slopus/codex-keybored/cnc/vendor_response/2026-07-18_JLCCNC_laser_marking/CM2-002_LASER_PLACEMENT_PREVIEW_RevB.png

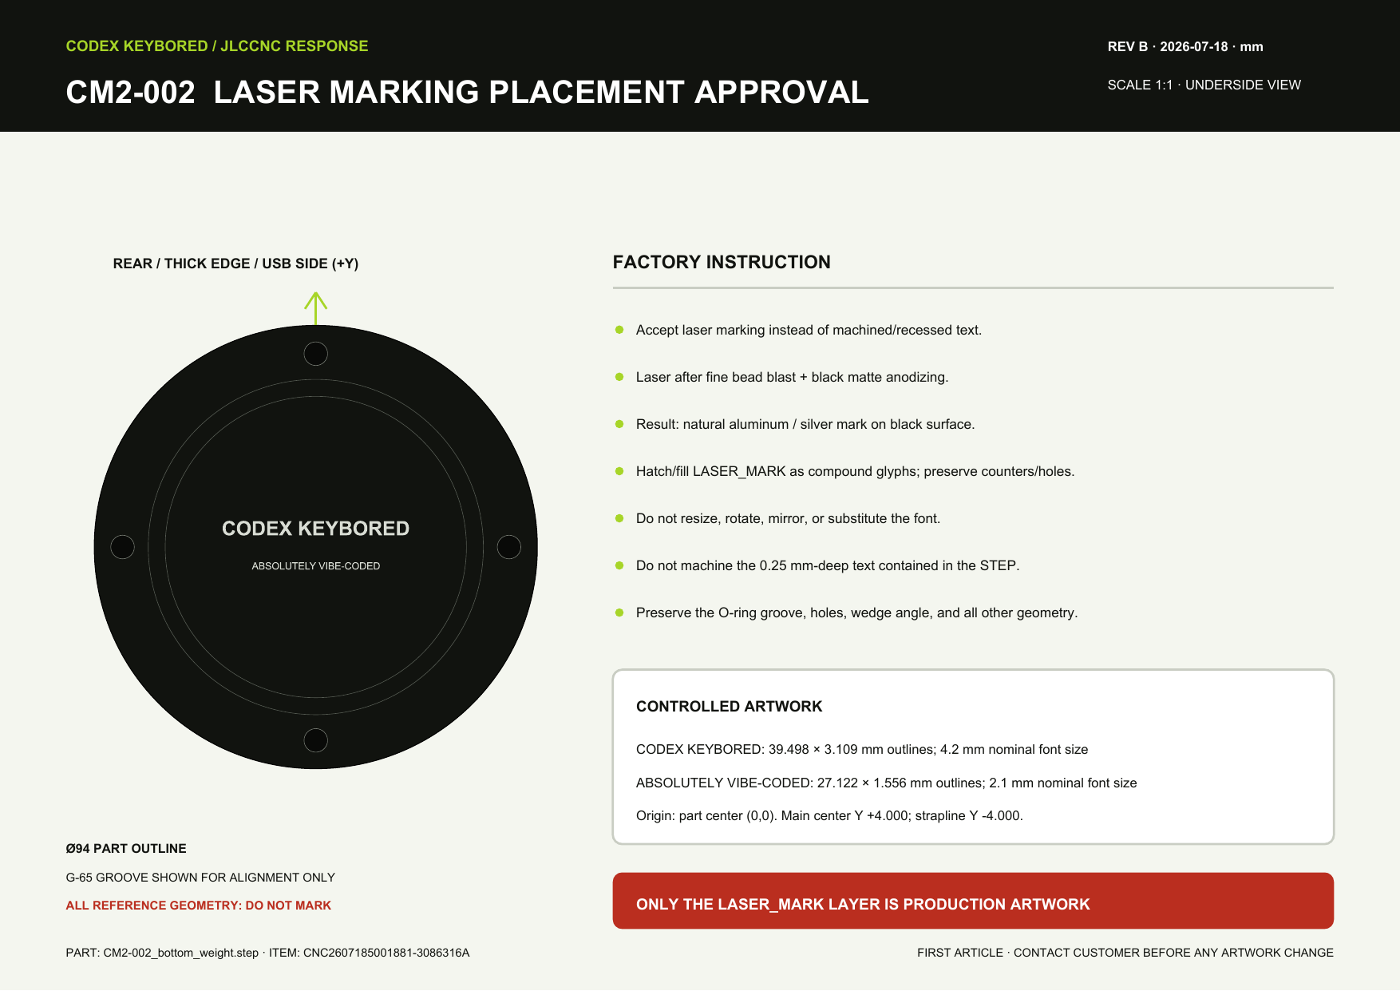
cnc/vendor_response/2026-07-18_JLCCNC_laser_marking/CM2-002_LASER_PLACEMENT_PREVIEW_RevB.png
