slopus/codex-keybored/docs/assets/jlcpcb/cart_pcb_cnc.png

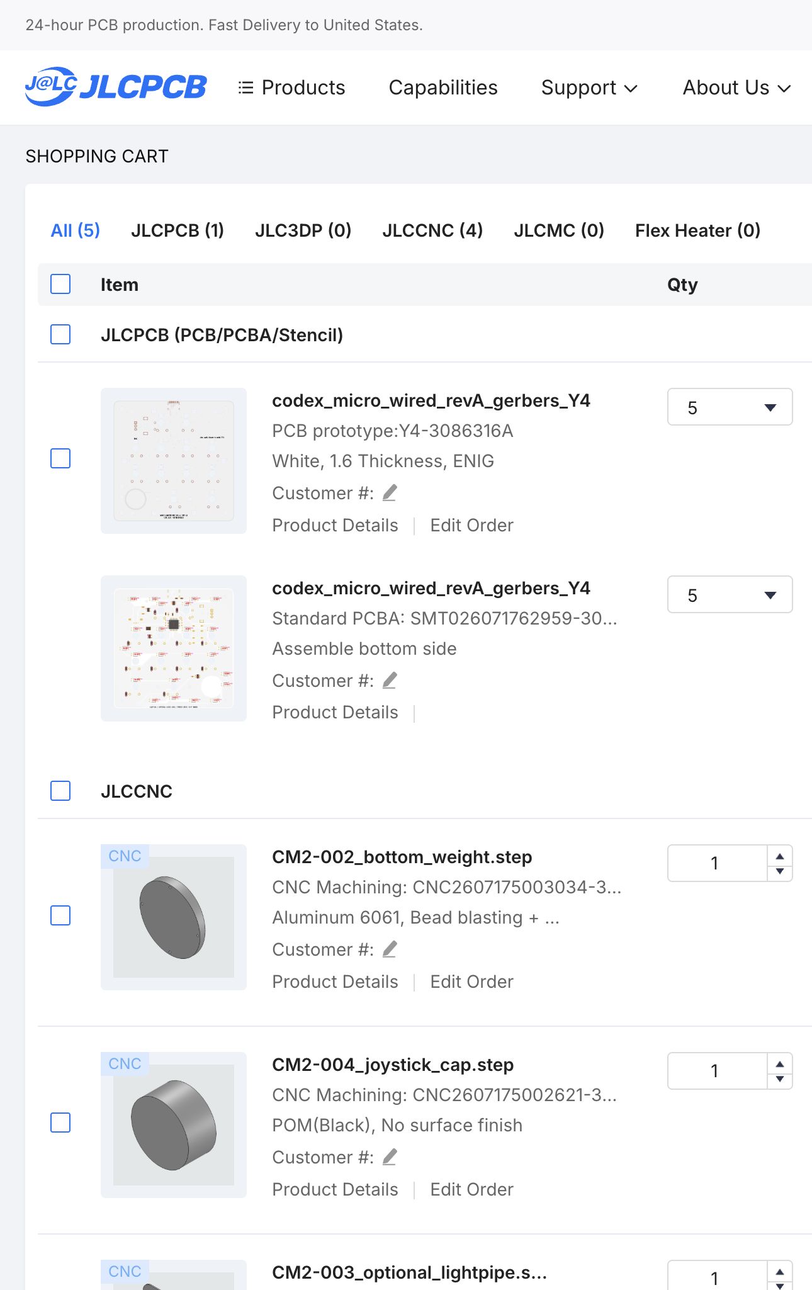
docs/assets/jlcpcb/cart_pcb_cnc.png
