slopus/codex-keybored/docs/assets/jlcpcb/cart_summary_total.png

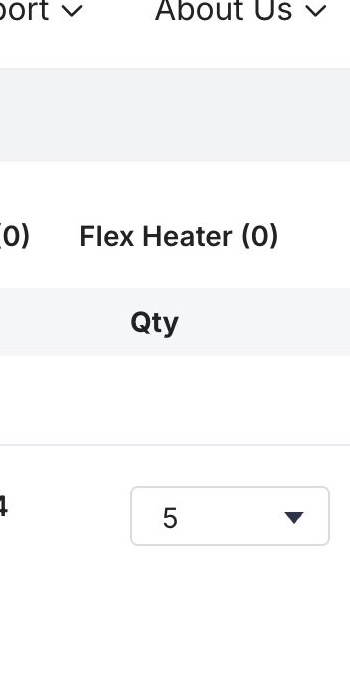
docs/assets/jlcpcb/cart_summary_total.png
