slopus/codex-keybored/docs/assets/jlcpcb/pcb_quote_config_full.png

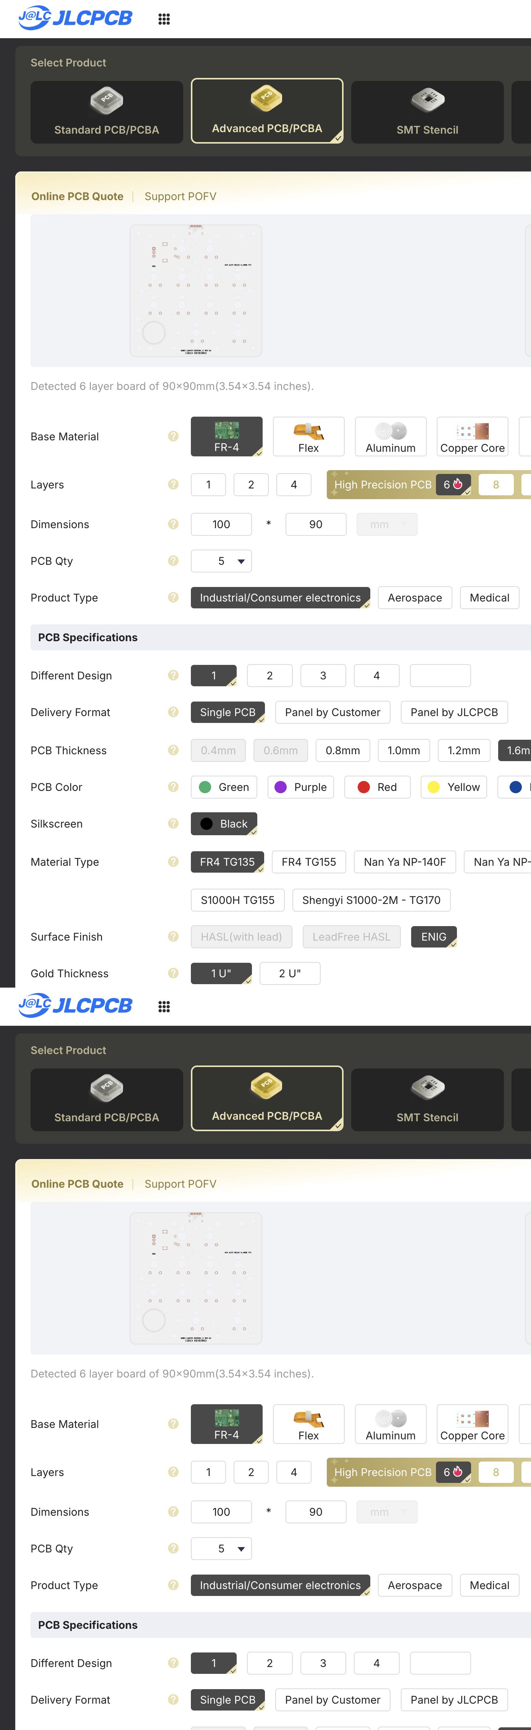
docs/assets/jlcpcb/pcb_quote_config_full.png
