slopus/codex-keybored/docs/assets/jlcpcb/pcba_final_quote.png

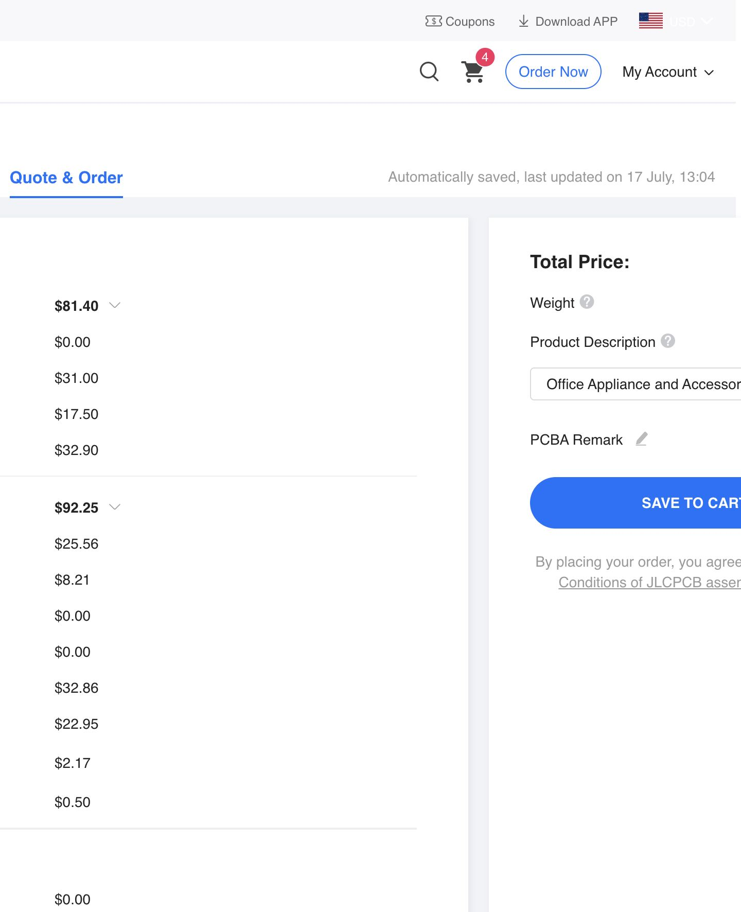
docs/assets/jlcpcb/pcba_final_quote.png
