slopus/codex-keybored/docs/assets/jlcpcb/pcba_final_quote_right.png

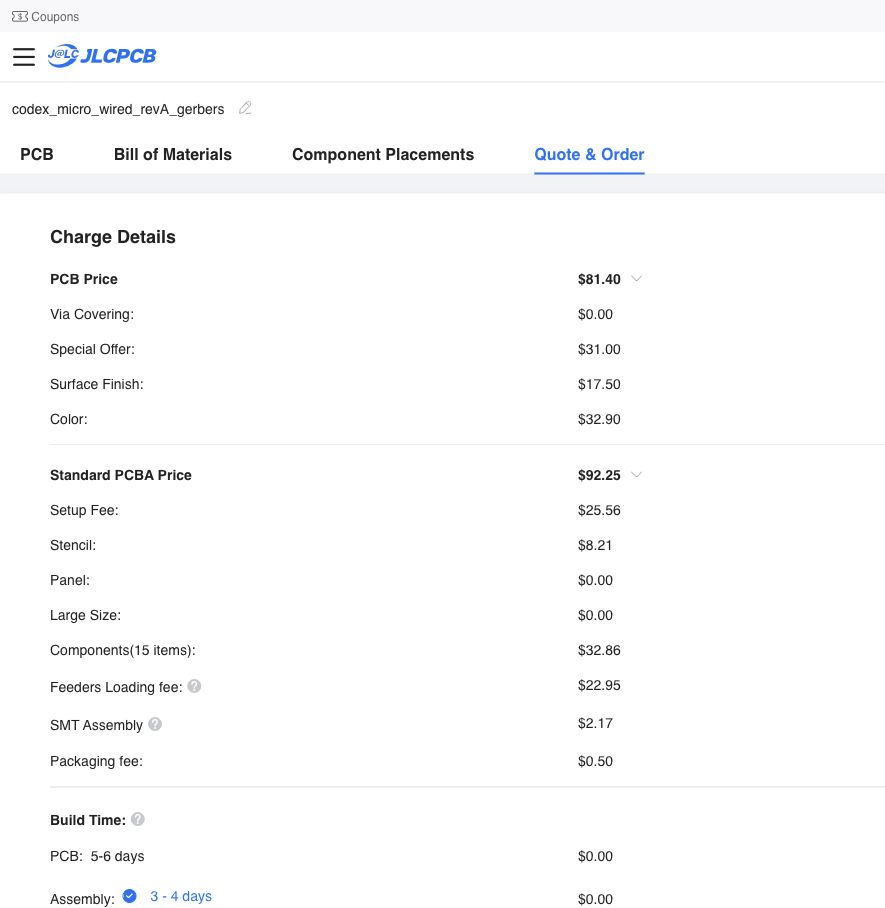
docs/assets/jlcpcb/pcba_final_quote_right.png
