slopus/codex-keybored/docs/assets/jlcpcb/pcba_final_total.png

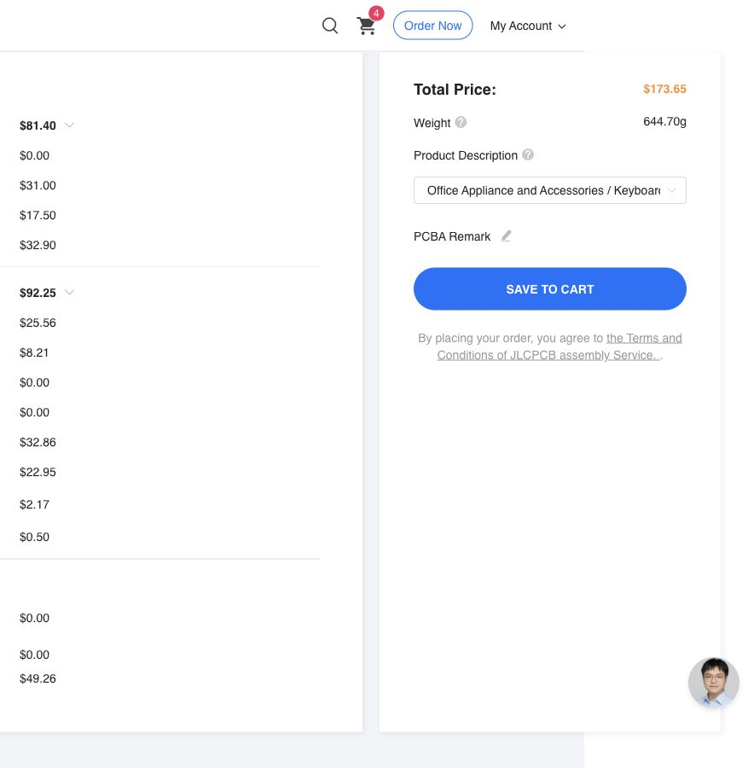
docs/assets/jlcpcb/pcba_final_total.png
