slopus/codex-keybored/docs/assets/jlcpcb/pcba_placement.png

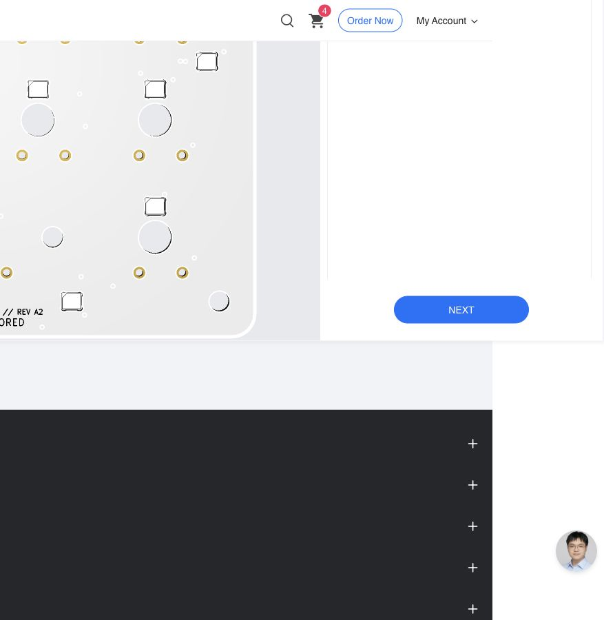
docs/assets/jlcpcb/pcba_placement.png
