slopus/codex-keybored/docs/assets/jlcpcb/turnkey_pcba_options.png

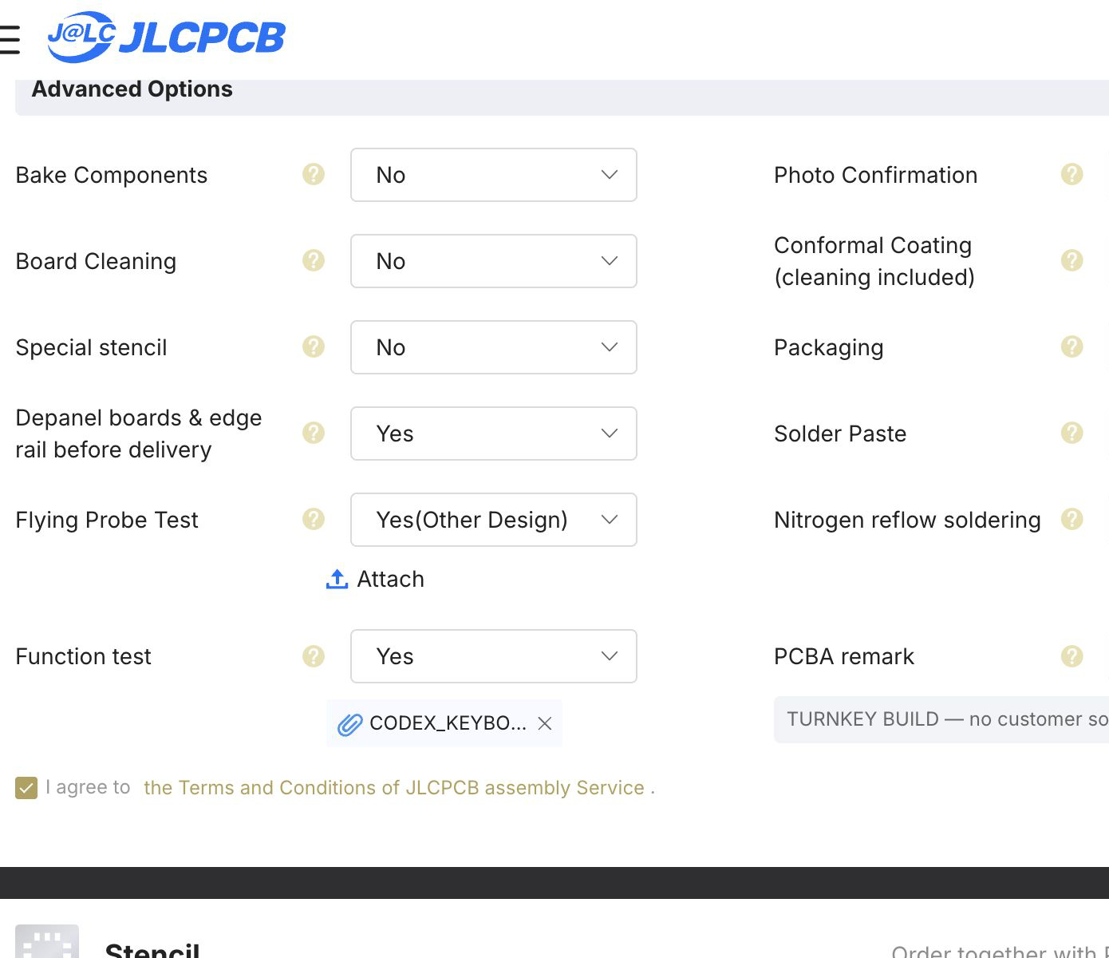
docs/assets/jlcpcb/turnkey_pcba_options.png
