slopus/codex-keybored/docs/assets/jlcpcb/turnkey_pcba_options_full.png

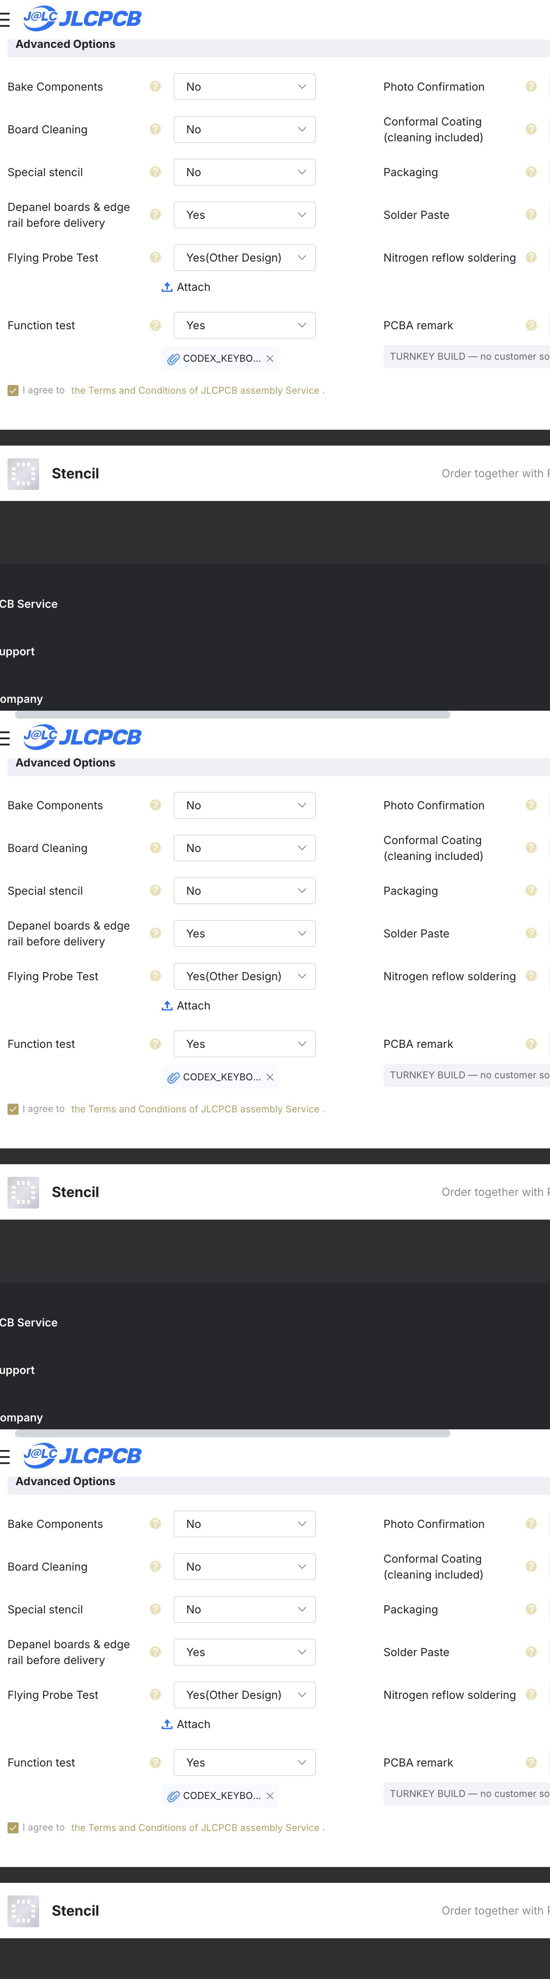
docs/assets/jlcpcb/turnkey_pcba_options_full.png
