slopus/codex-keybored/docs/assets/jlcpcb/turnkey_quote_total.png

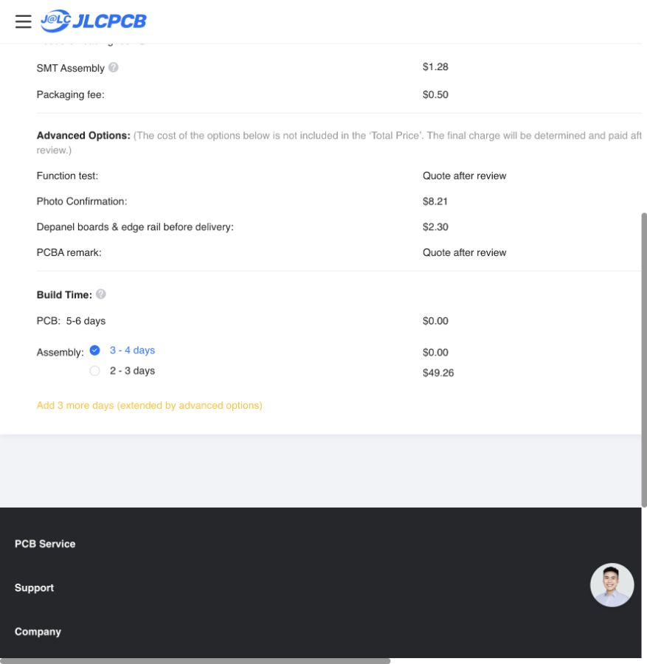
docs/assets/jlcpcb/turnkey_quote_total.png
