slopus/codex-keybored/docs/assets/pcb/keybored_bottom.png

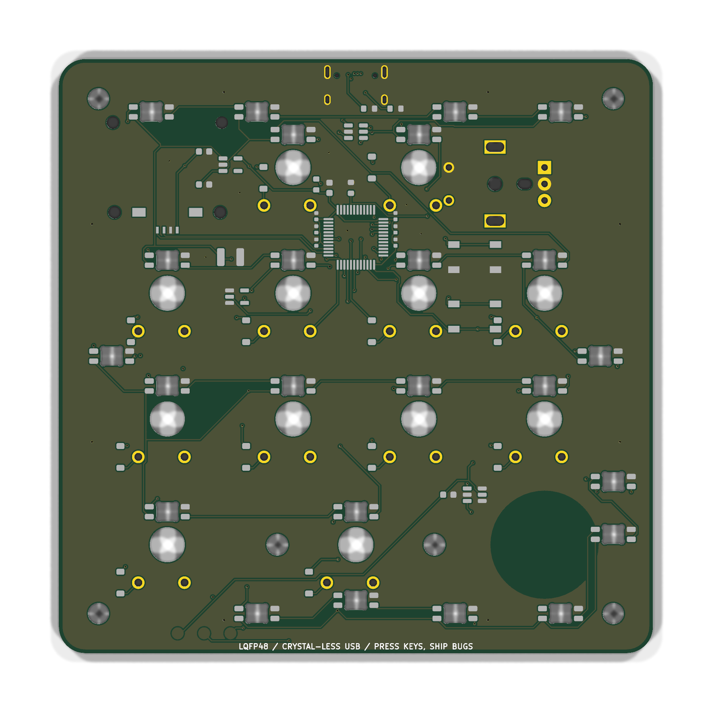
docs/assets/pcb/keybored_bottom.png
