slopus/codex-keybored/docs/assets/pcb/wired-reva-B-Cu.png

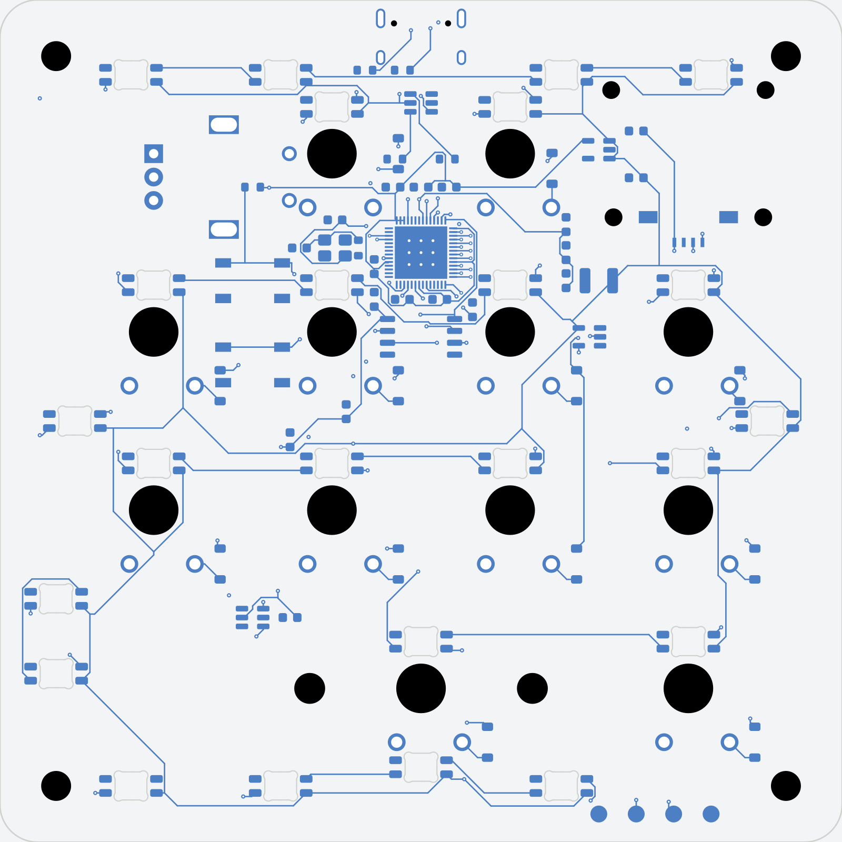
docs/assets/pcb/wired-reva-B-Cu.png
