slopus/codex-keybored/docs/assets/pcb/wired-reva-current-bottom.png

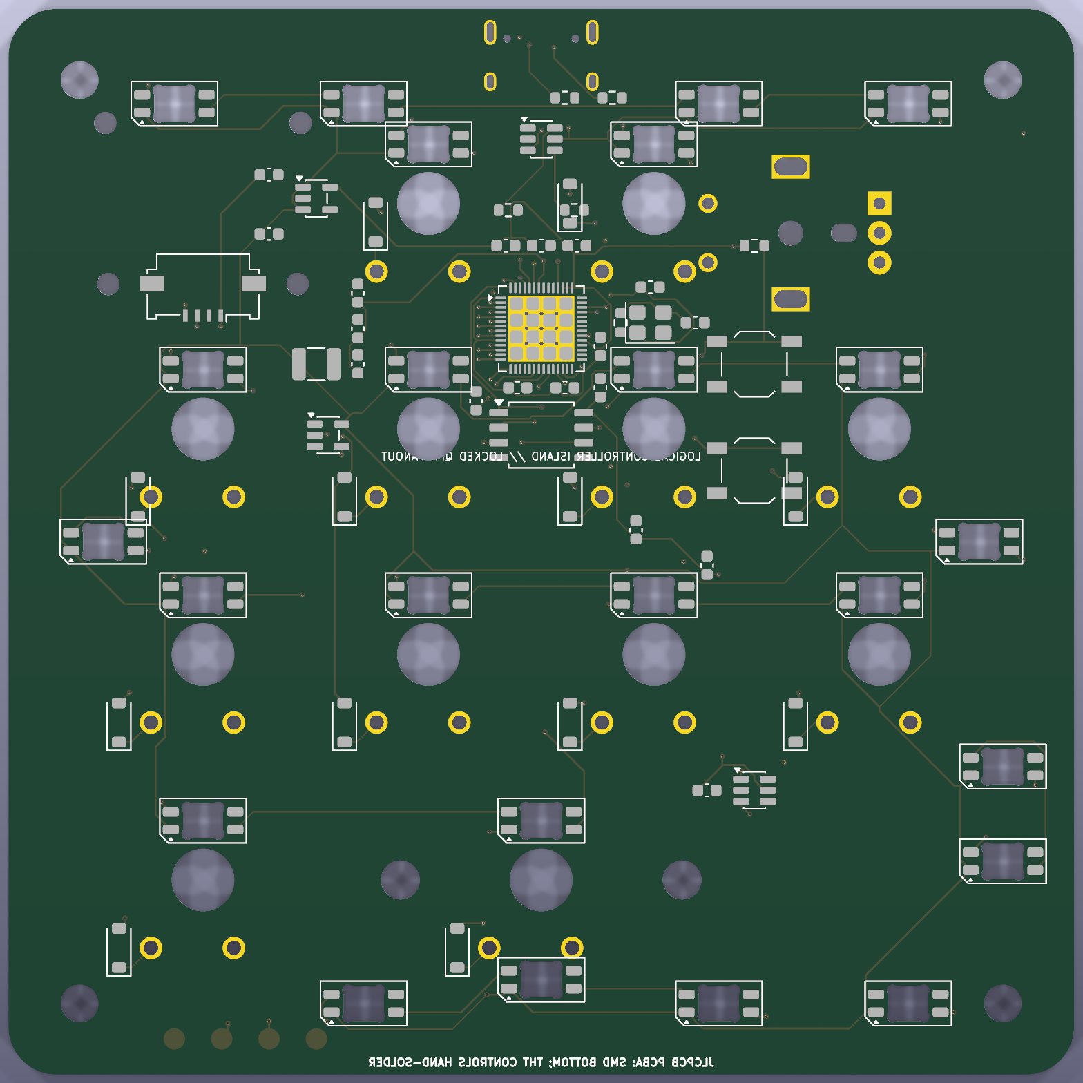
docs/assets/pcb/wired-reva-current-bottom.png
