slopus/codex-keybored/docs/assets/pcb/wired-reva-current-top.png

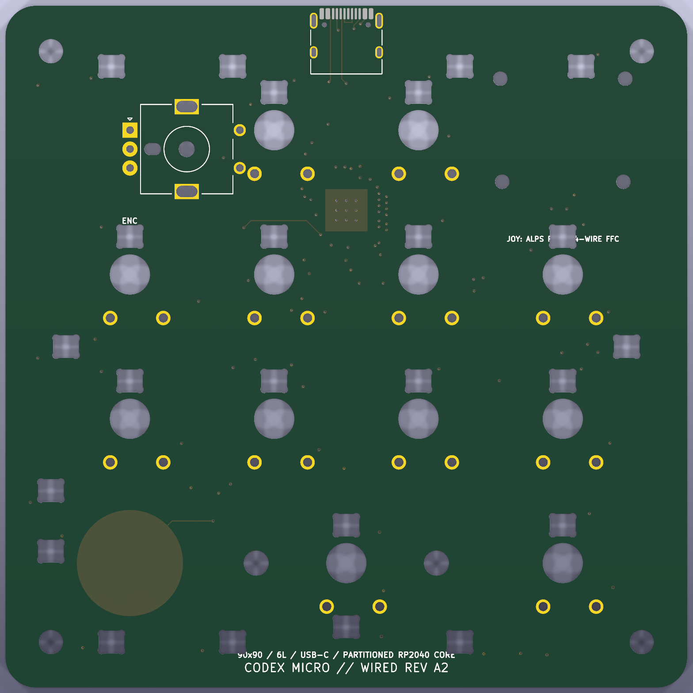
docs/assets/pcb/wired-reva-current-top.png
