slopus/codex-keybored/docs/assets/pcb/wired-reva-F-Cu.png

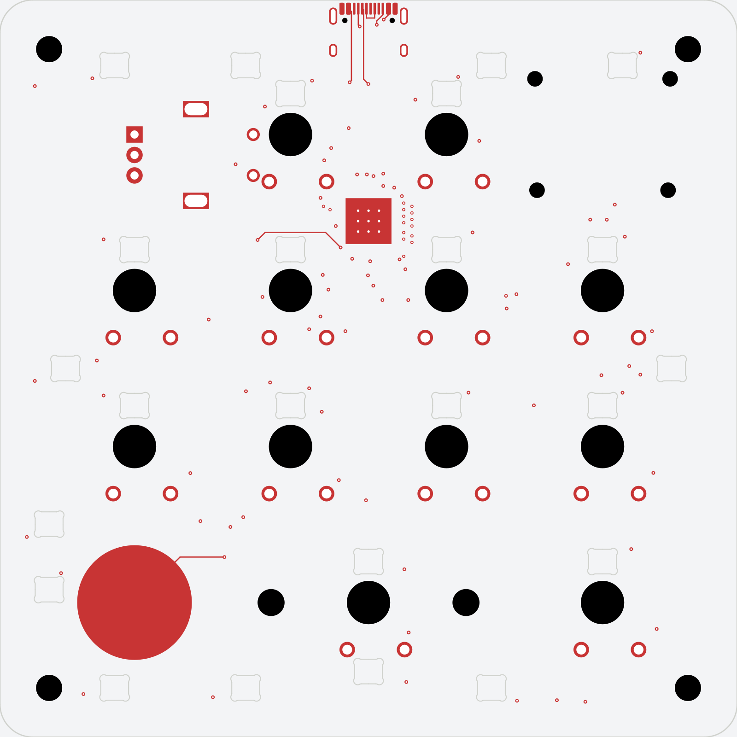
docs/assets/pcb/wired-reva-F-Cu.png
