slopus/codex-keybored/docs/assets/pcb/wired-reva-In1-Cu.png

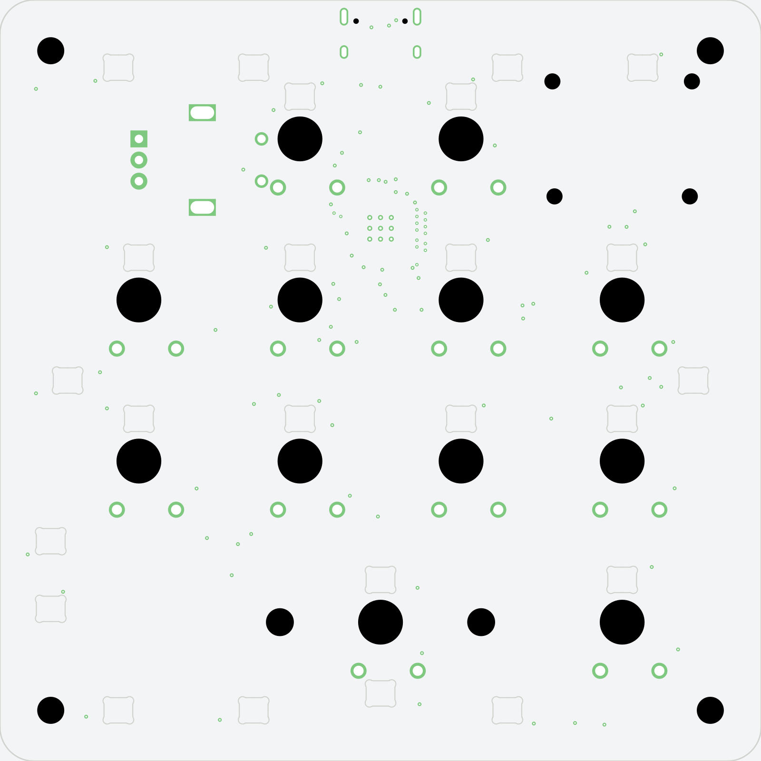
docs/assets/pcb/wired-reva-In1-Cu.png
