slopus/codex-keybored/docs/assets/pcb/wired-reva-In2-Cu.png

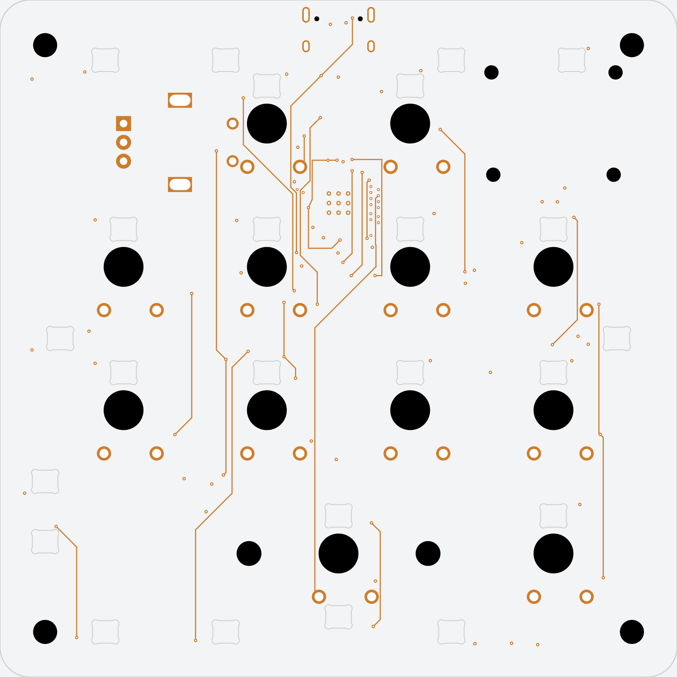
docs/assets/pcb/wired-reva-In2-Cu.png
