slopus/codex-keybored/docs/assets/pcb/wired-reva-In3-Cu.png

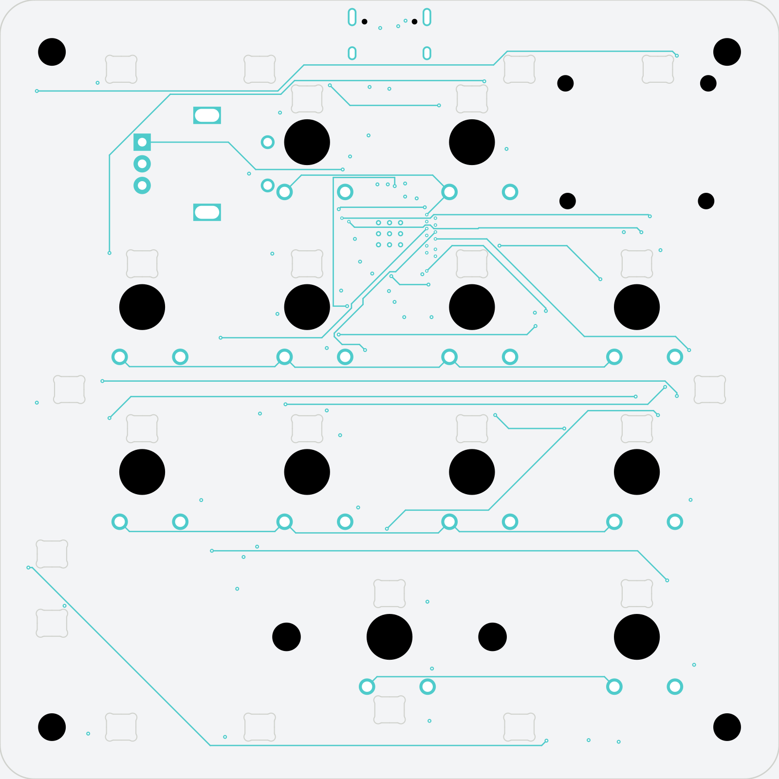
docs/assets/pcb/wired-reva-In3-Cu.png
