slopus/codex-keybored/docs/assets/renders/fusion-cm2-001-upper-housing.png

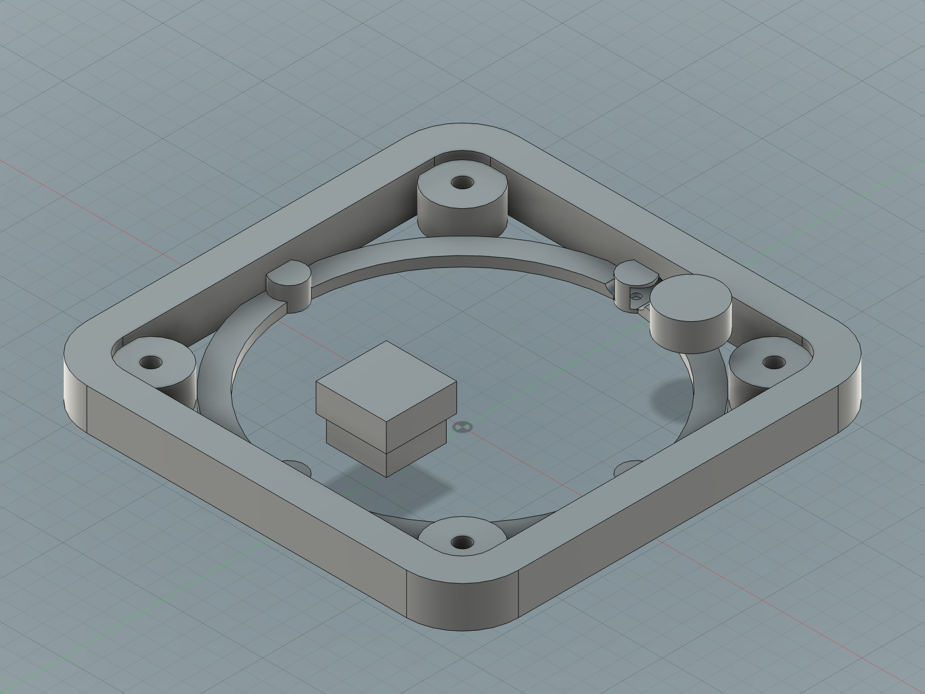
docs/assets/renders/fusion-cm2-001-upper-housing.png
