slopus/codex-keybored/docs/assets/renders/fusion-cm2-002-bottom-weight-side.png

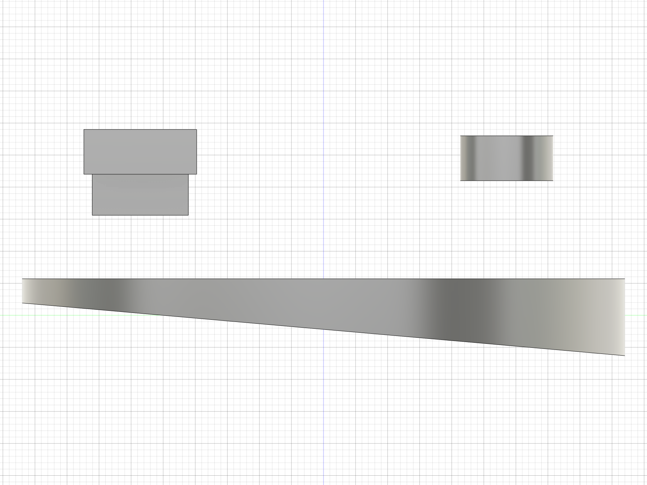
docs/assets/renders/fusion-cm2-002-bottom-weight-side.png
