slopus/codex-keybored/docs/assets/renders/fusion-cm2-002-bottom-weight.png

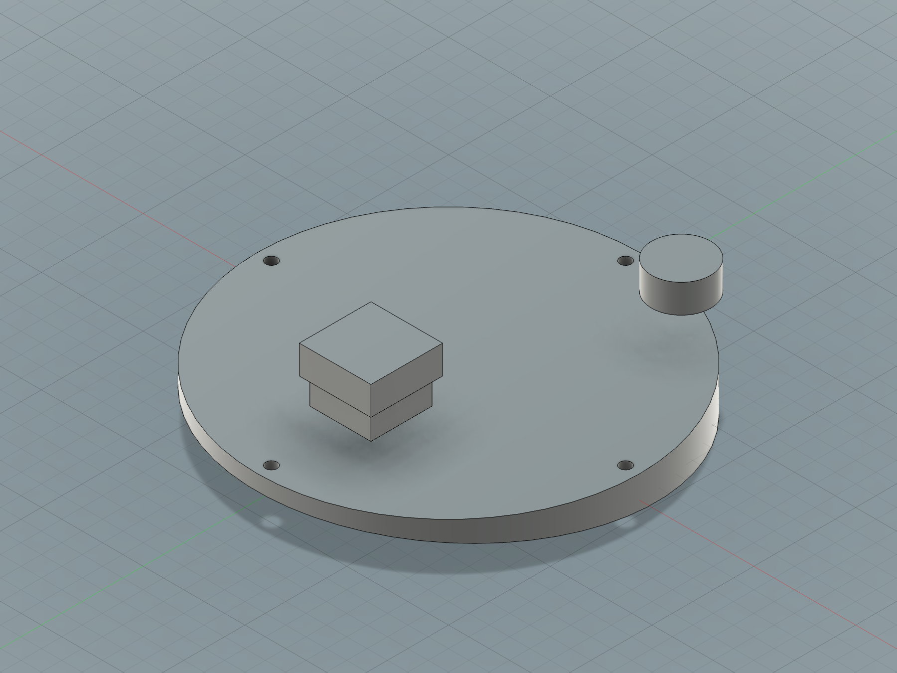
docs/assets/renders/fusion-cm2-002-bottom-weight.png
