slopus/codex-keybored/docs/assets/renders/fusion-cm2-004-joystick-cap.png

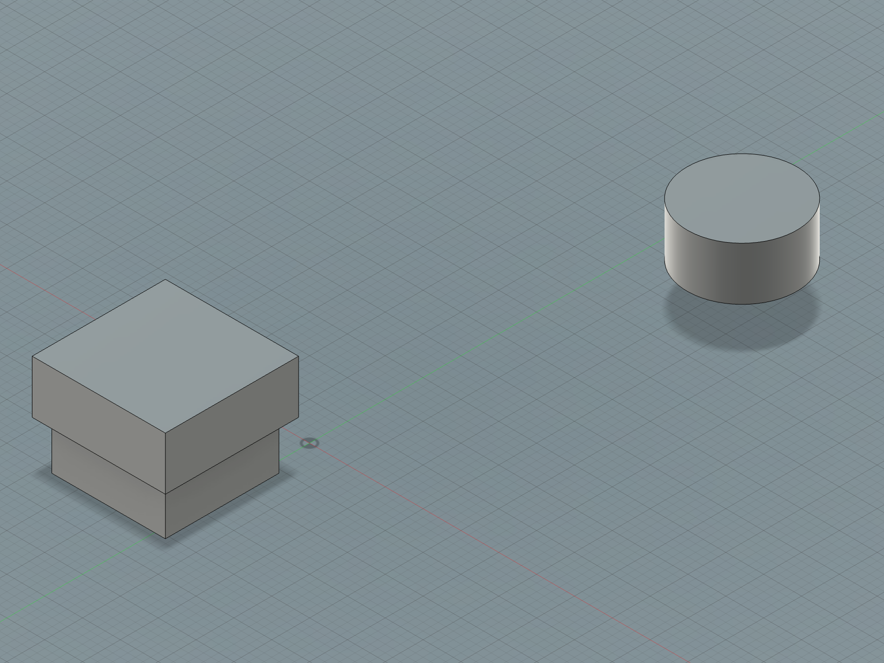
docs/assets/renders/fusion-cm2-004-joystick-cap.png
