slopus/codex-keybored/docs/assets/renders/kicad-wired-reva-top.png

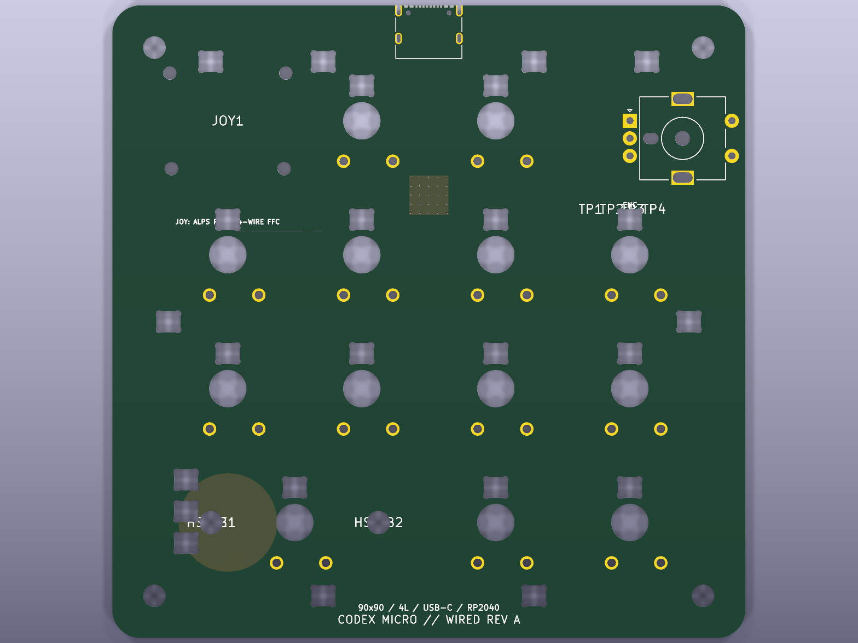
docs/assets/renders/kicad-wired-reva-top.png
