slopus/codex-keybored/docs/assets/renders/revb-cm2-001-upper.png

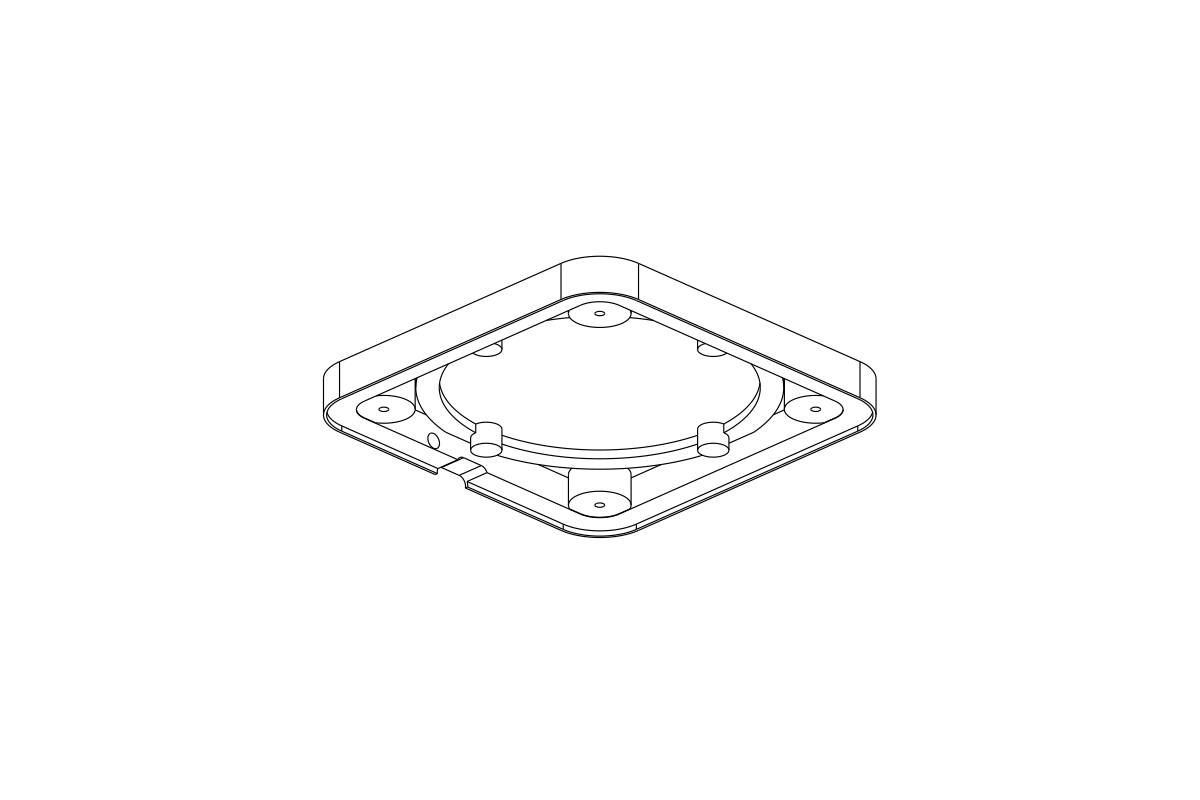
docs/assets/renders/revb-cm2-001-upper.png
