slopus/codex-keybored/docs/assets/renders/revb-cm2-002-bottom.png

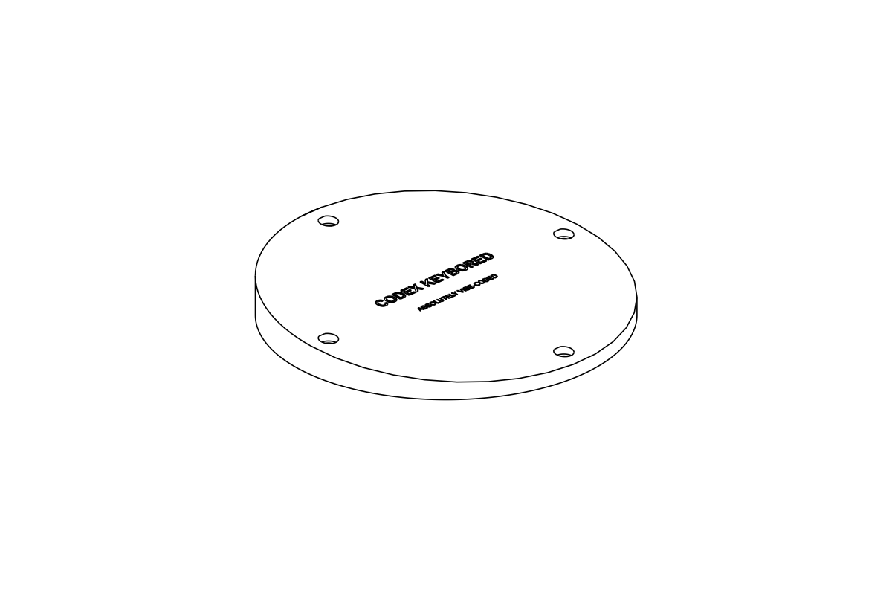
docs/assets/renders/revb-cm2-002-bottom.png
