slopus/codex-keybored/docs/assets/renders/revb-cm2-004-cap.png

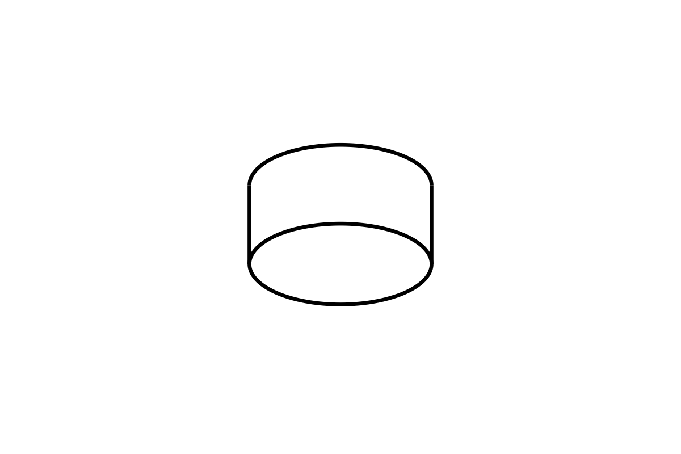
docs/assets/renders/revb-cm2-004-cap.png
