slopus/codex-keybored/docs/assets/renders/revb-jlcmc-g65-oring.png

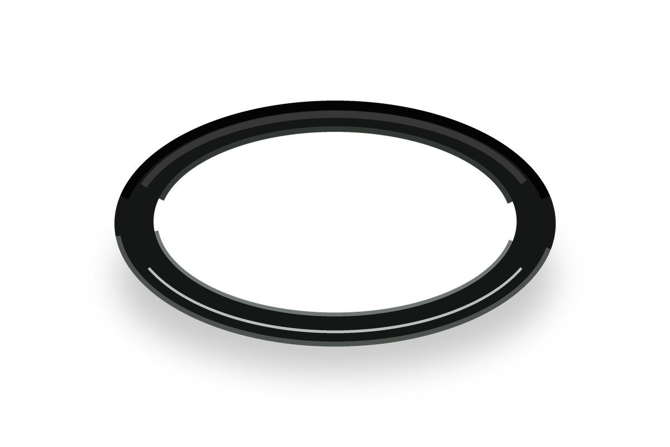
docs/assets/renders/revb-jlcmc-g65-oring.png
