slopus/codex-keybored/docs/assets/screenshots/jlccnc-added-to-cart.png

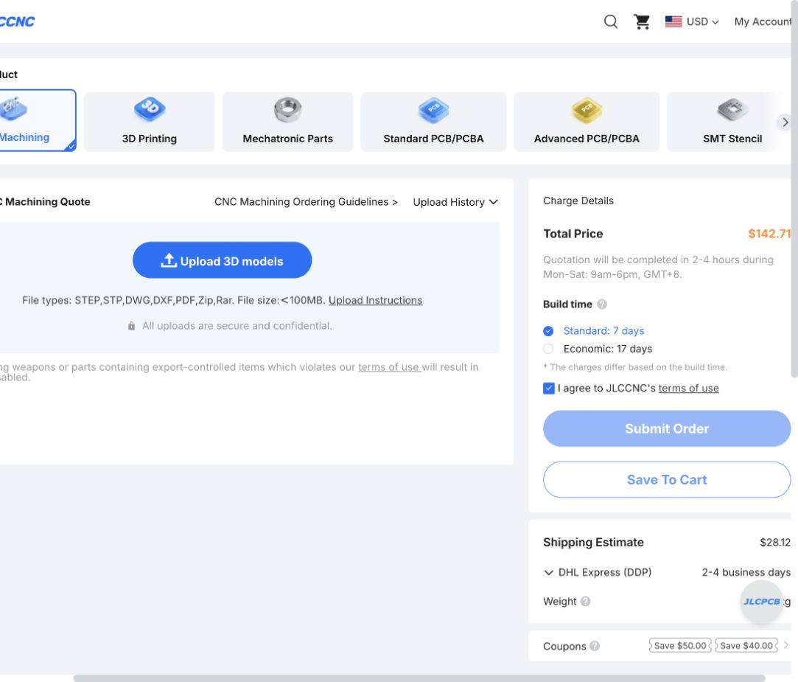
docs/assets/screenshots/jlccnc-added-to-cart.png
