slopus/codex-keybored/docs/assets/screenshots/jlccnc-batch-default-aluminum.png

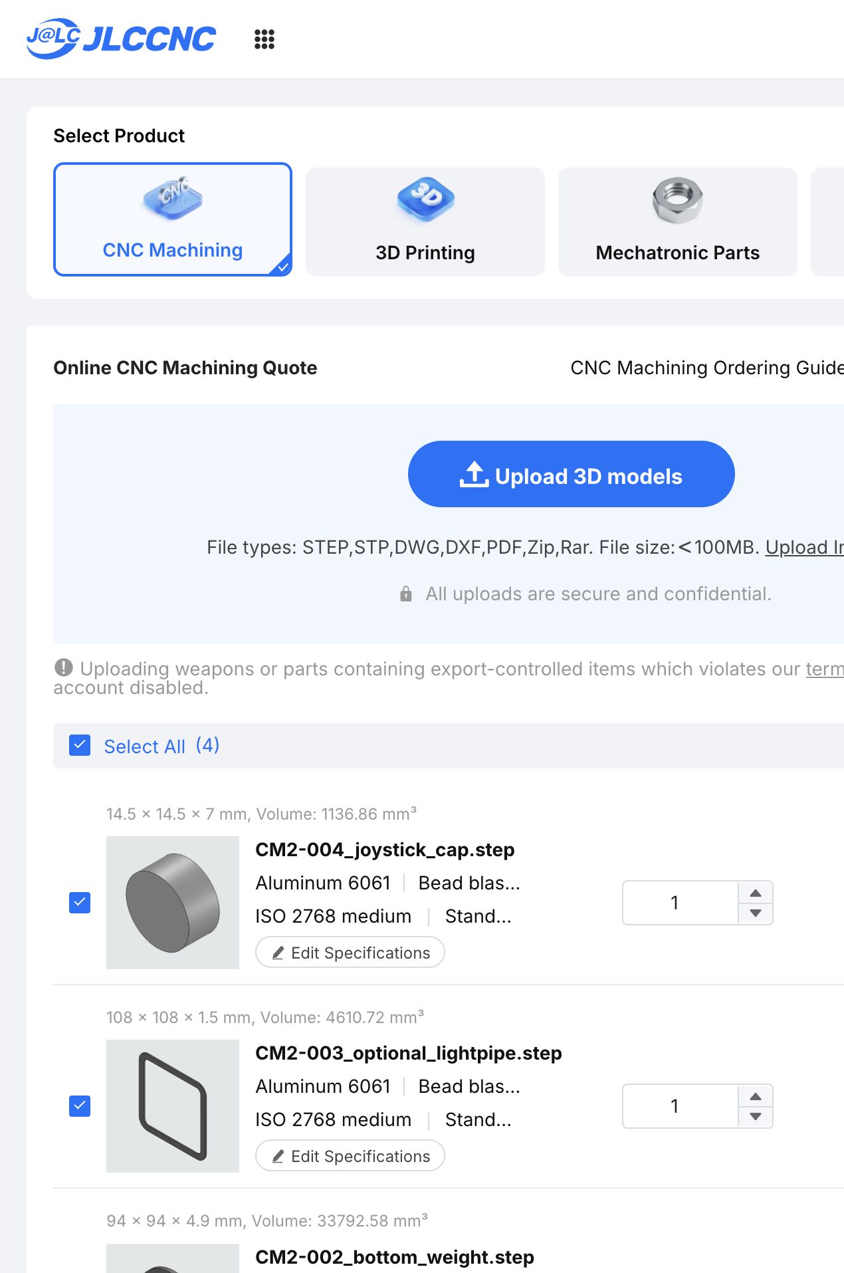
docs/assets/screenshots/jlccnc-batch-default-aluminum.png
