slopus/codex-keybored/docs/assets/screenshots/jlccnc-clean-cart-4-items.png

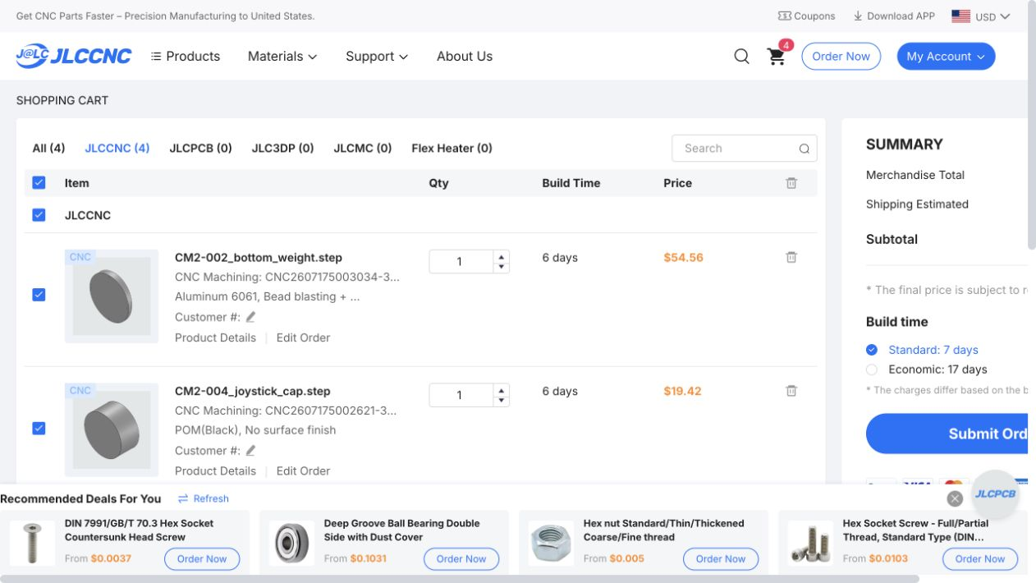
docs/assets/screenshots/jlccnc-clean-cart-4-items.png
