slopus/codex-keybored/docs/assets/screenshots/jlccnc-final-quote-summary.png

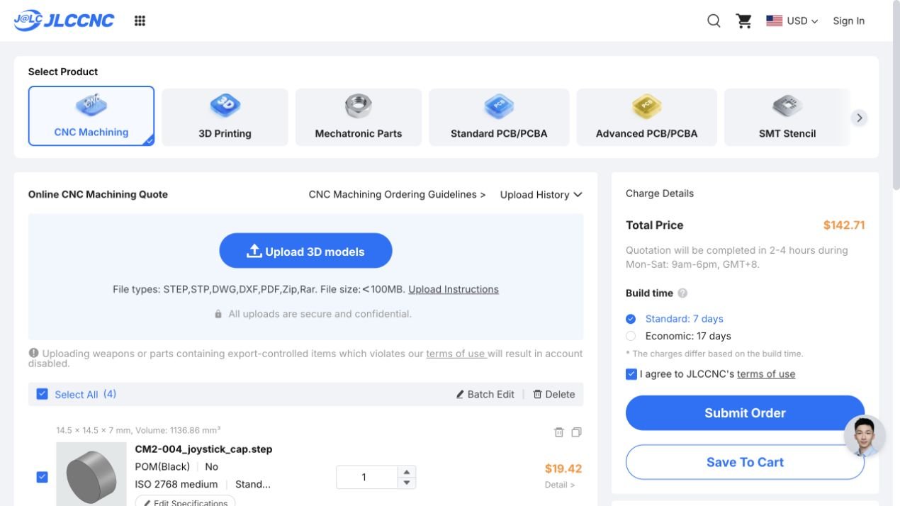
docs/assets/screenshots/jlccnc-final-quote-summary.png
