slopus/codex-keybored/docs/assets/screenshots/jlccnc-shipping-estimate.png

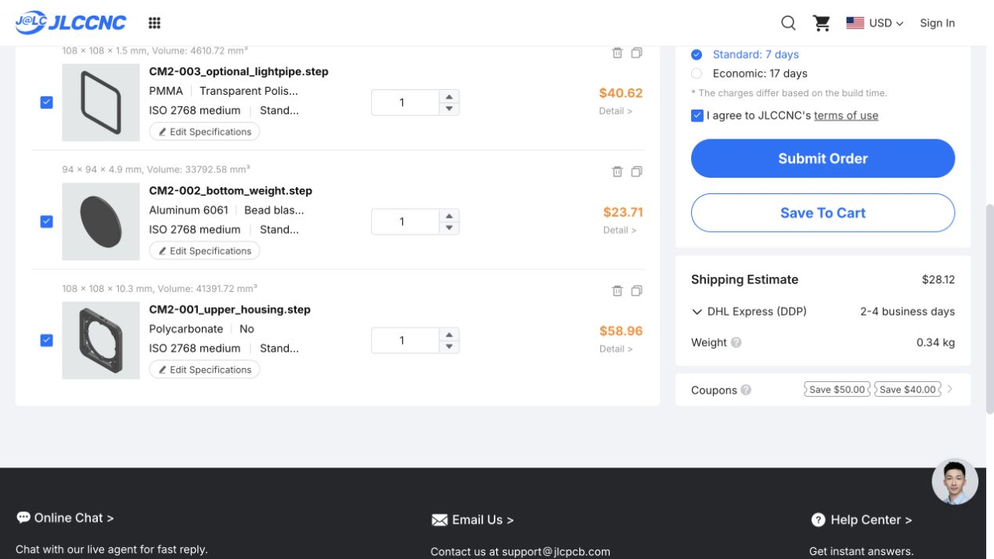
docs/assets/screenshots/jlccnc-shipping-estimate.png
