slopus/codex-keybored/docs/assets/screenshots/jlcmc-g65-ring-cart.png

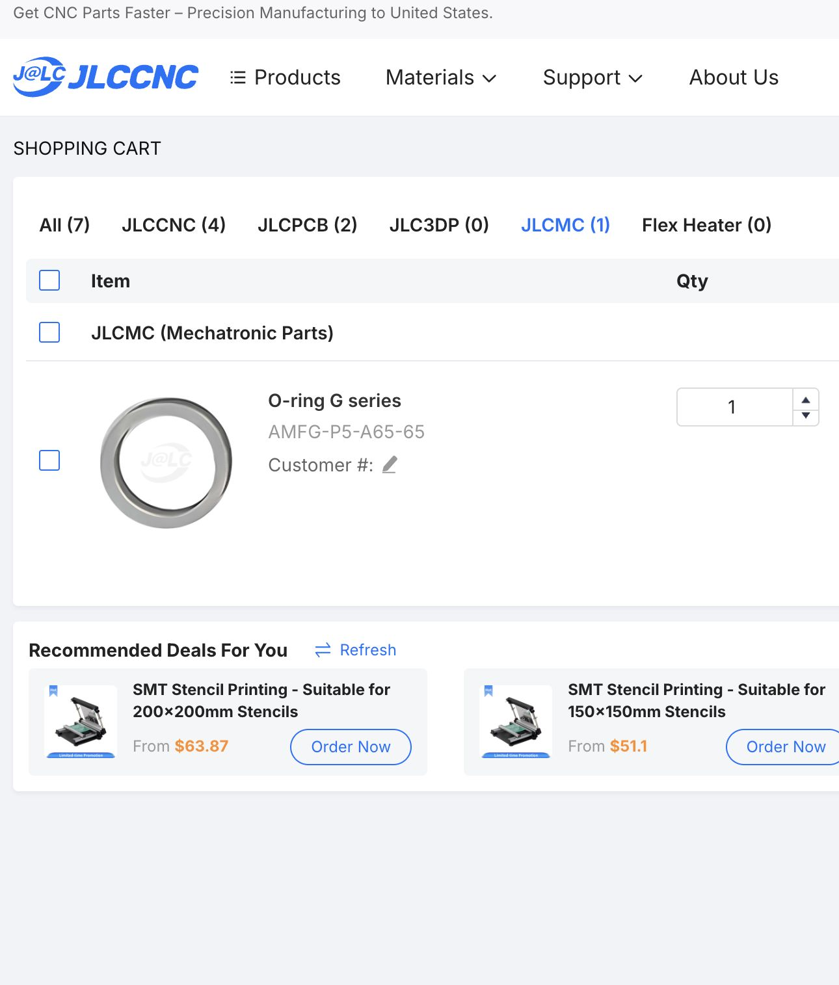
docs/assets/screenshots/jlcmc-g65-ring-cart.png
