slopus/codex-keybored/docs/assets/screenshots/openai-codex-micro-gallery-exploded.png

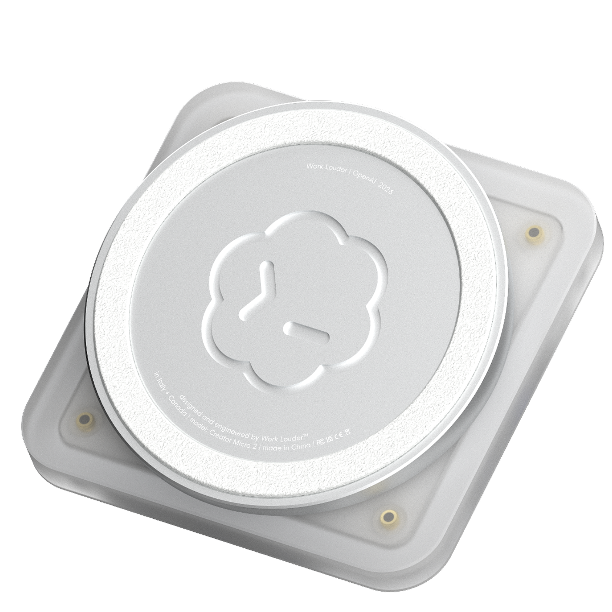
docs/assets/screenshots/openai-codex-micro-gallery-exploded.png
