slopus/codex-keybored/docs/assets/screenshots/openai-codex-micro-gallery-primary.png

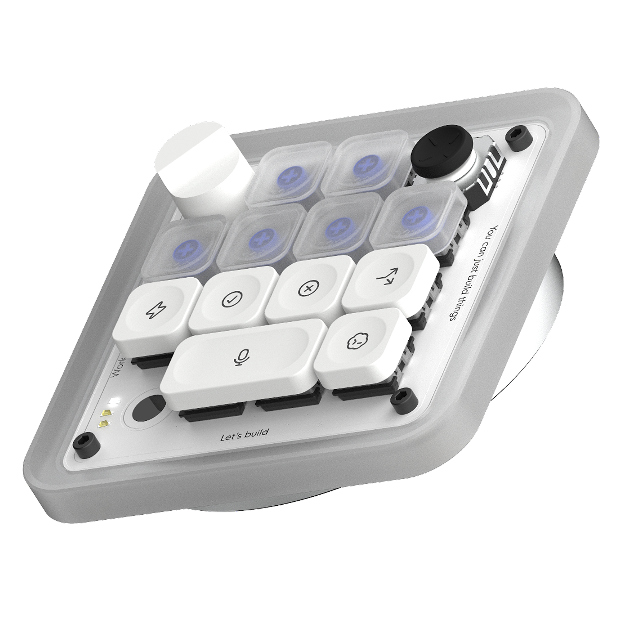
docs/assets/screenshots/openai-codex-micro-gallery-primary.png
