slopus/codex-keybored/docs/assets/screenshots/openai-codex-micro-product-gallery-2.png

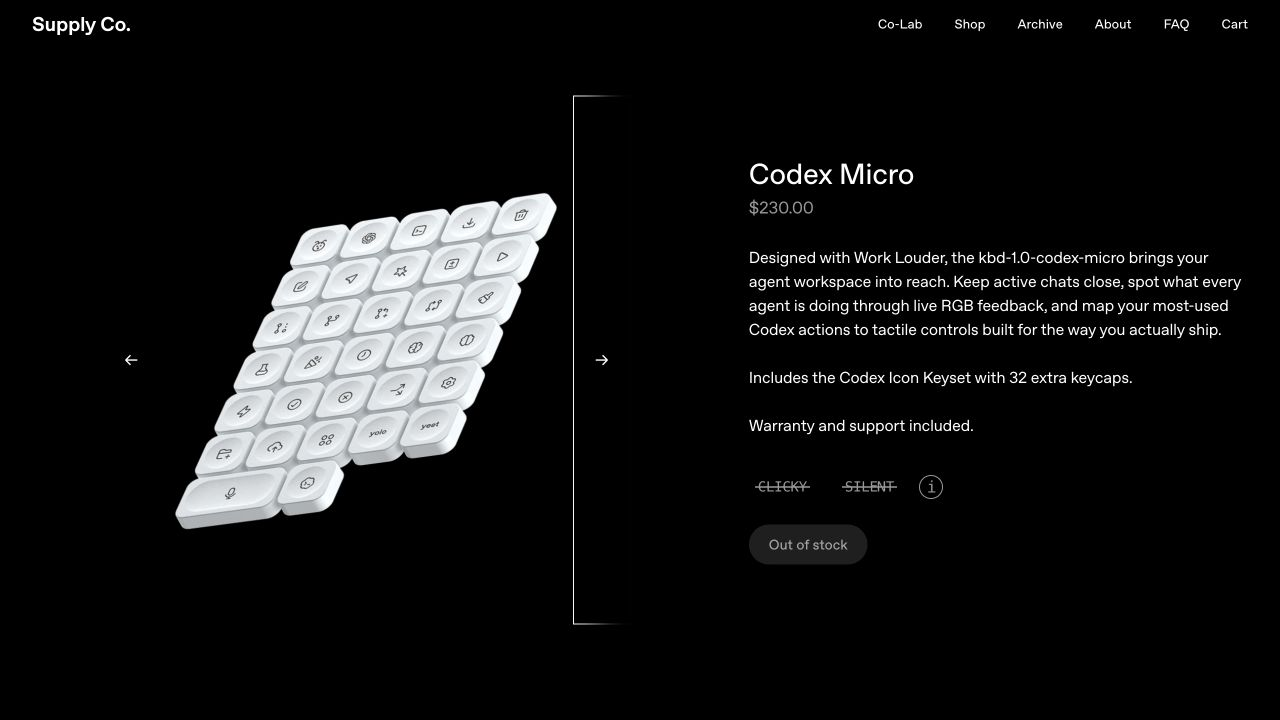
docs/assets/screenshots/openai-codex-micro-product-gallery-2.png
