slopus/codex-keybored/docs/assets/screenshots/openai-codex-micro-product-gallery-3.png

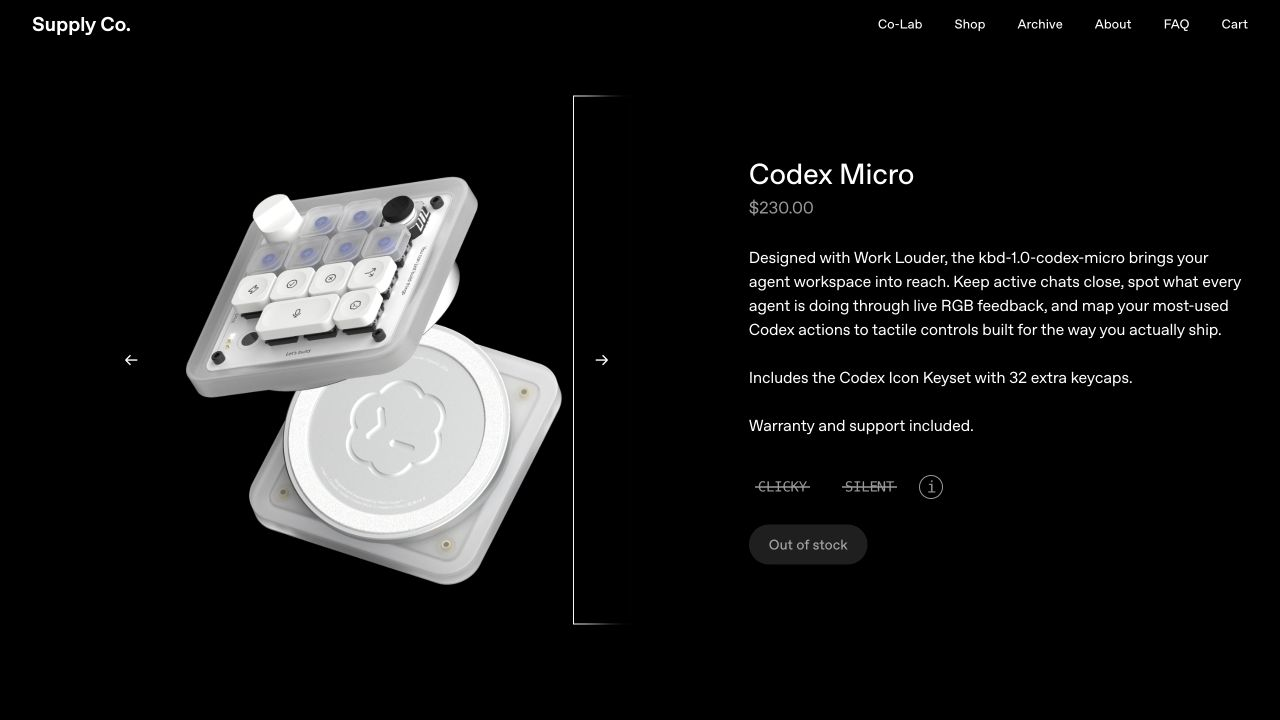
docs/assets/screenshots/openai-codex-micro-product-gallery-3.png
