slopus/codex-keybored/docs/assets/screenshots/openai-codex-micro-product-gallery-4.png

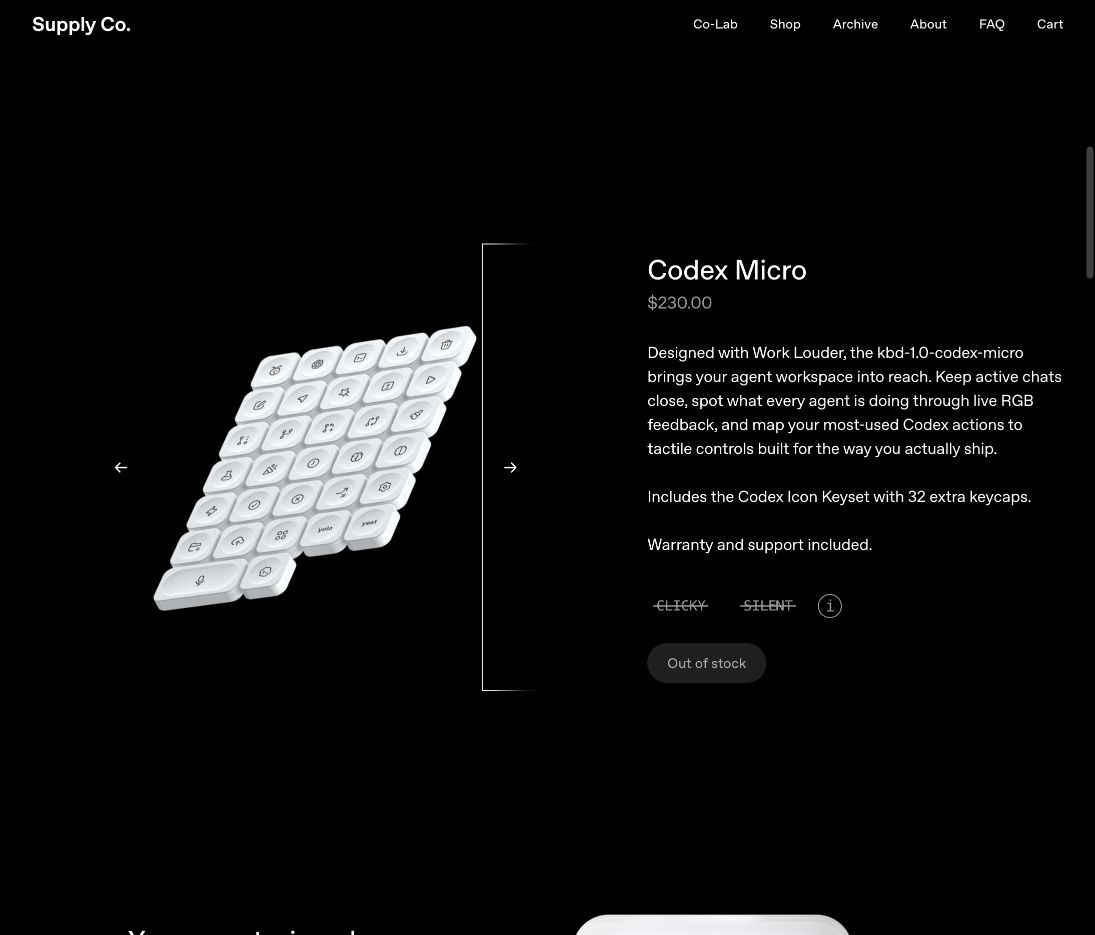
docs/assets/screenshots/openai-codex-micro-product-gallery-4.png
