slopus/codex-keybored/docs/assets/screenshots/openai-codex-micro-product-gallery.png

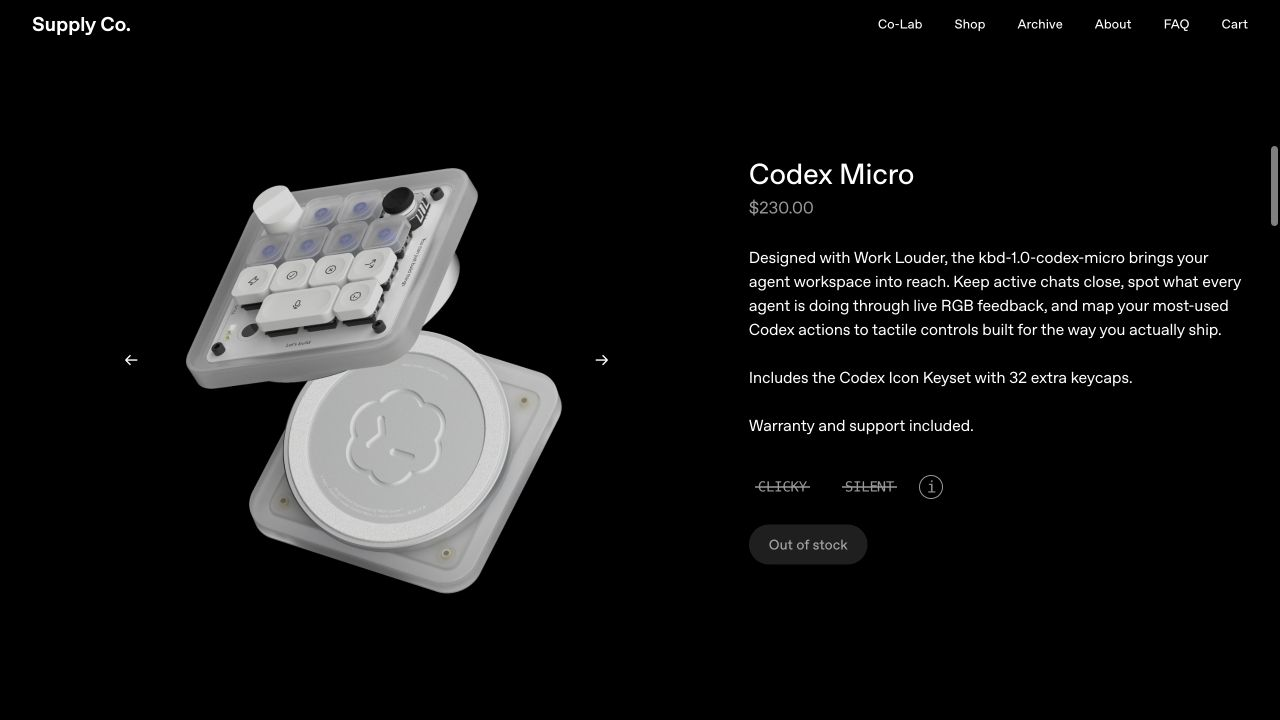
docs/assets/screenshots/openai-codex-micro-product-gallery.png
