slopus/codex-keybored/docs/assets/screenshots/worklouder-cm2-angle-1.jpg

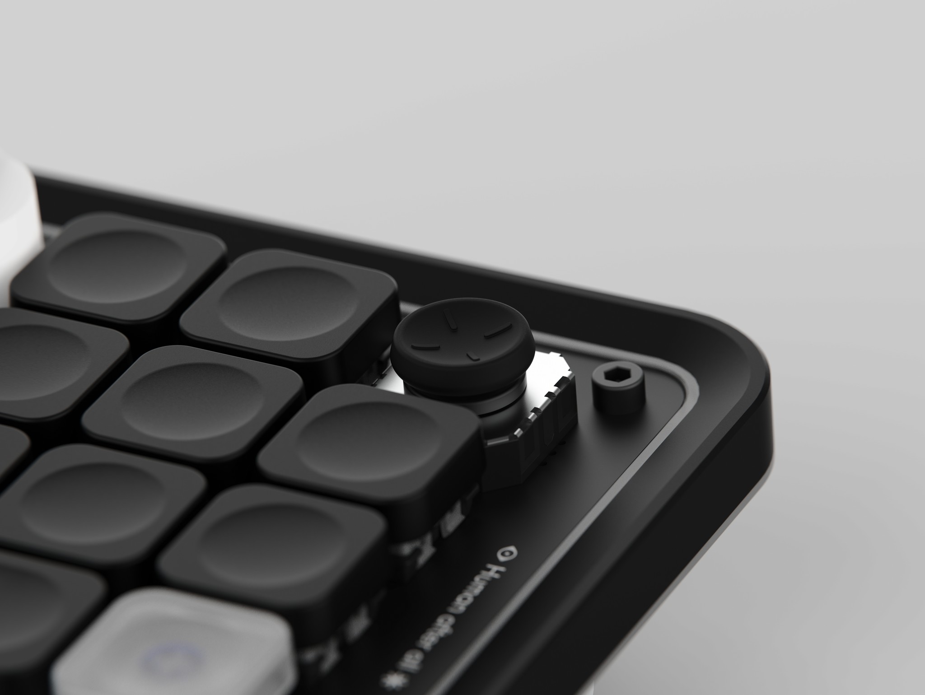
docs/assets/screenshots/worklouder-cm2-angle-1.jpg
