slopus/codex-keybored/docs/assets/screenshots/worklouder-cm2-angle-2.jpg

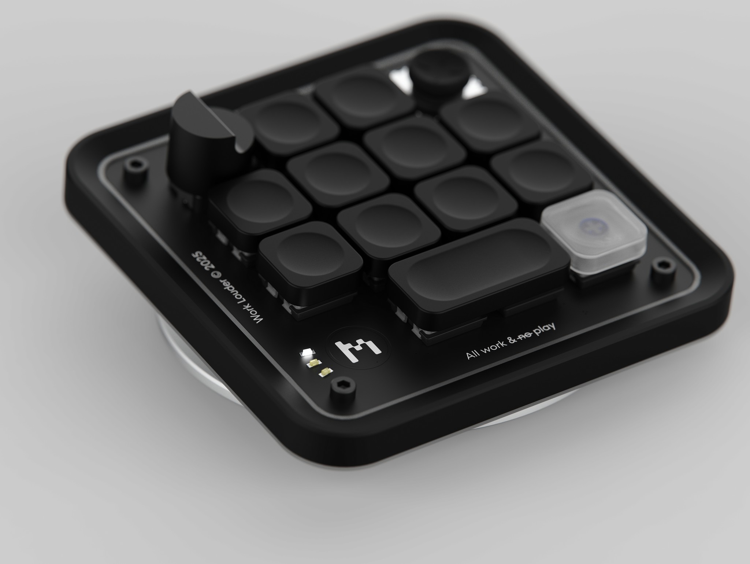
docs/assets/screenshots/worklouder-cm2-angle-2.jpg
