slopus/codex-keybored/docs/assets/screenshots/worklouder-cm2-angle-4.jpg

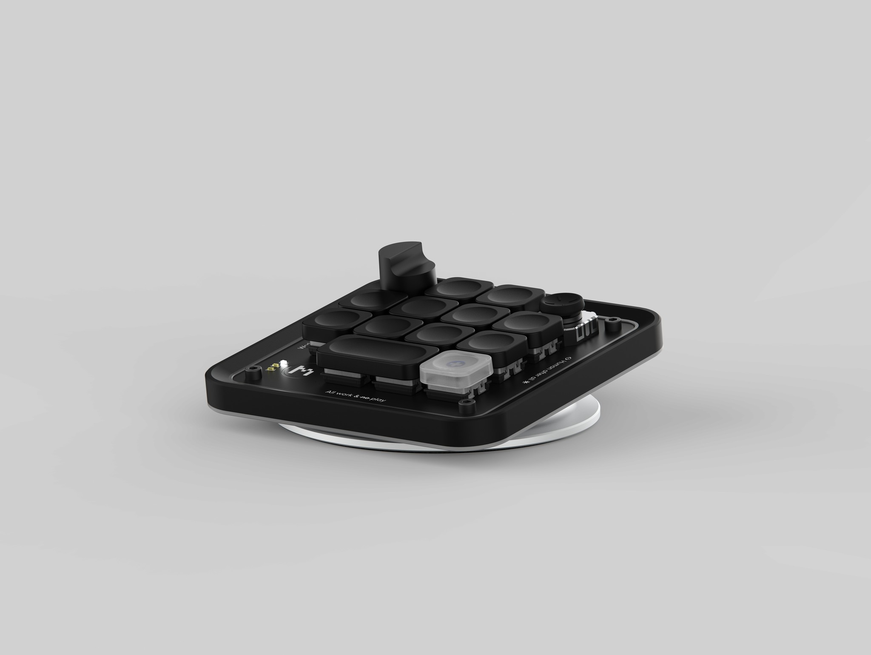
docs/assets/screenshots/worklouder-cm2-angle-4.jpg
