slopus/codex-keybored/docs/assets/screenshots/worklouder-cm2-angle-5.jpg

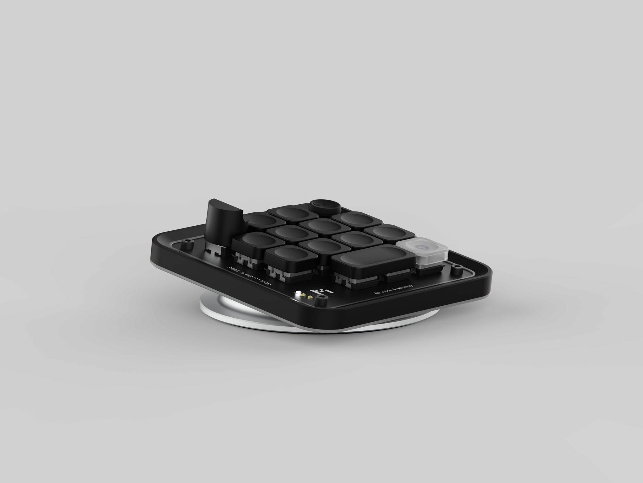
docs/assets/screenshots/worklouder-cm2-angle-5.jpg
