slopus/codex-keybored/docs/assets/screenshots/jlccnc-final-materials-qty1.png

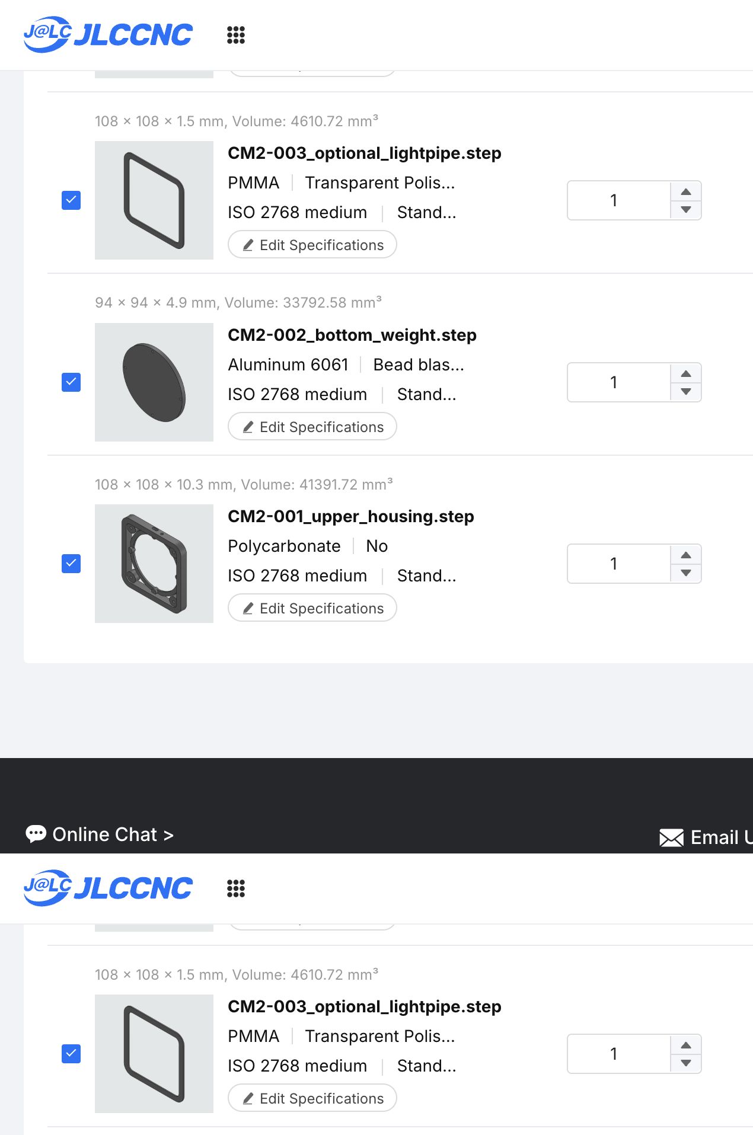
docs/assets/screenshots/jlccnc-final-materials-qty1.png
