slopus/codex-keybored/docs/assets/renders/fusion-codex-assembly-iso.png

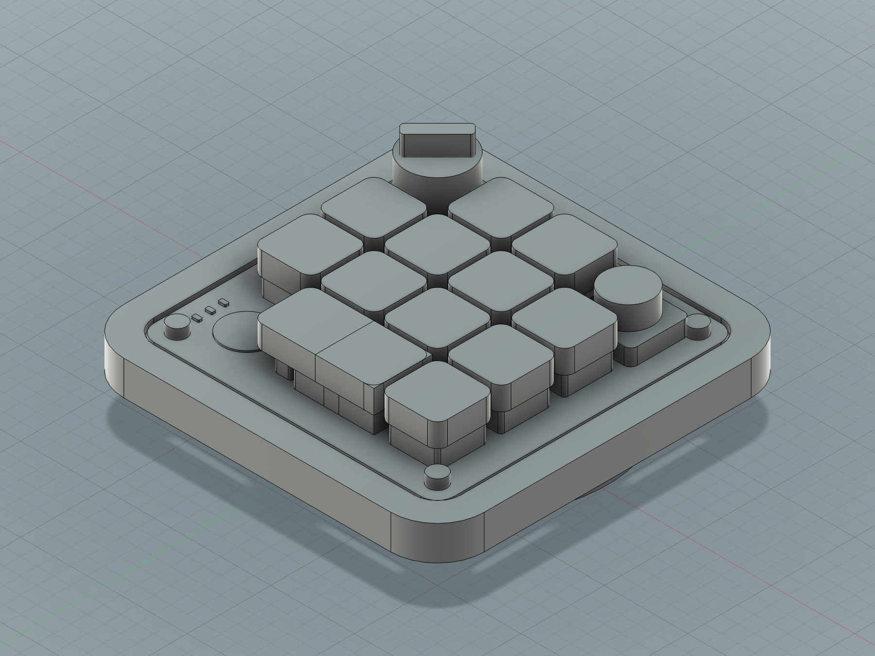
docs/assets/renders/fusion-codex-assembly-iso.png
