slopus/codex-keybored/cnc/drawings/CM2_CNC_Drawing_Pack_RevA.pdf

## CODEX MICRO / CNC DRAWING PACK

# CM2-001 UPPER HOUSING

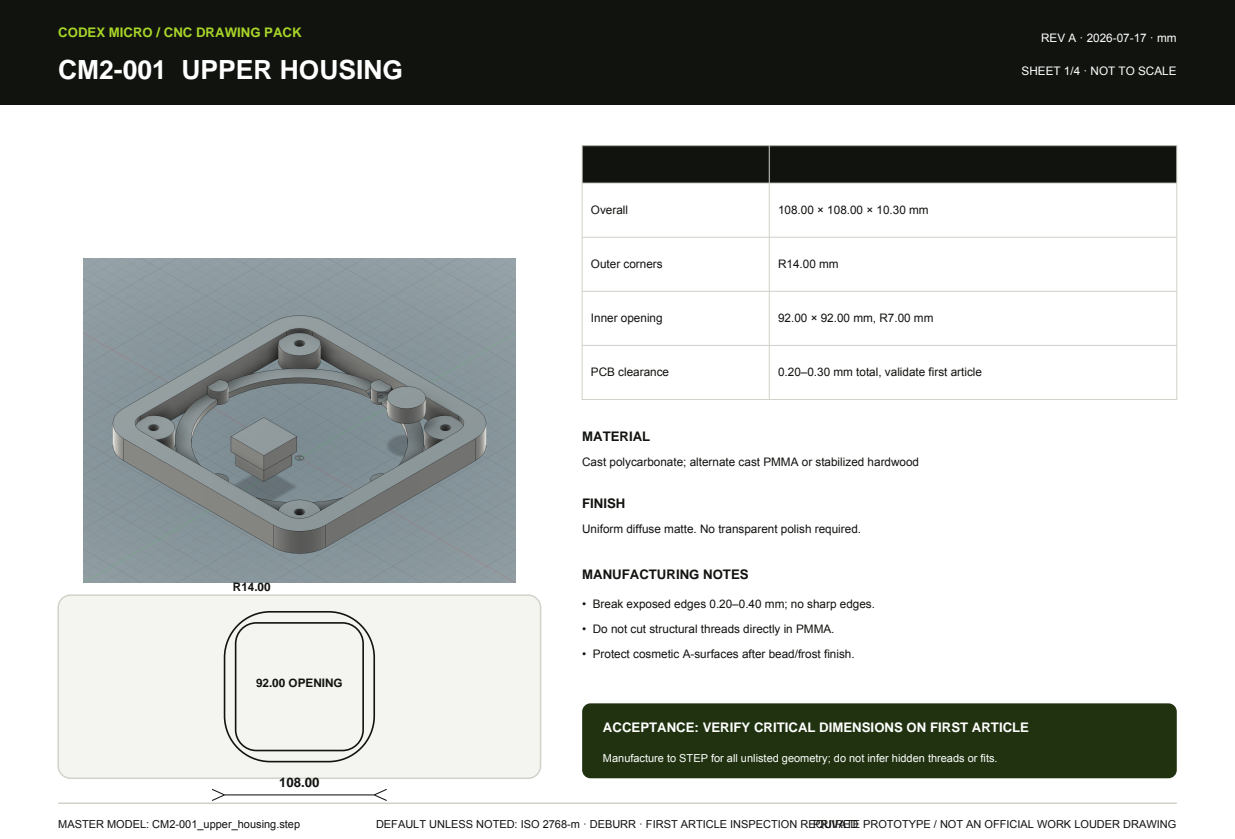
[picture p89: page 1]
REV A · 2026-07-17 · mm; MASTER MODEL: CM2-001_upper_housing.step; DEFAULT UNLESS NOTED: ISO 2768-m · DEBURR · FIRST ARTICLE INSPECTION REQUIRED PRIVATE PROTOTYPE / NOT AN OFFICIAL WORK LOUDER DRAWING; 92.00 OPENING; MATERIAL; FINISH; MANUFACTURING NOTES

SHEET 1/4 · NOT TO SCALE

PROPERTY | CONTROLLED REQUIREMENT

Overall | 108.00 × 108.00 × 10.30 mm

Outer corners | R14.00 mm

Inner opening | 92.00 × 92.00 mm, R7.00 mm

PCB clearance | 0.20–0.30 mm total, validate first article

Cast polycarbonate; alternate cast PMMA or stabilized hardwood

Uniform diffuse matte. No transparent polish required.

• Break exposed edges 0.20–0.40 mm; no sharp edges.

• Do not cut structural threads directly in PMMA.

• Protect cosmetic A-surfaces after bead/frost finish.

ACCEPTANCE: VERIFY CRITICAL DIMENSIONS ON FIRST ARTICLE

Manufacture to STEP for all unlisted geometry; do not infer hidden threads or fits.

# CM2-002 ANGLED BOTTOM WEIGHT

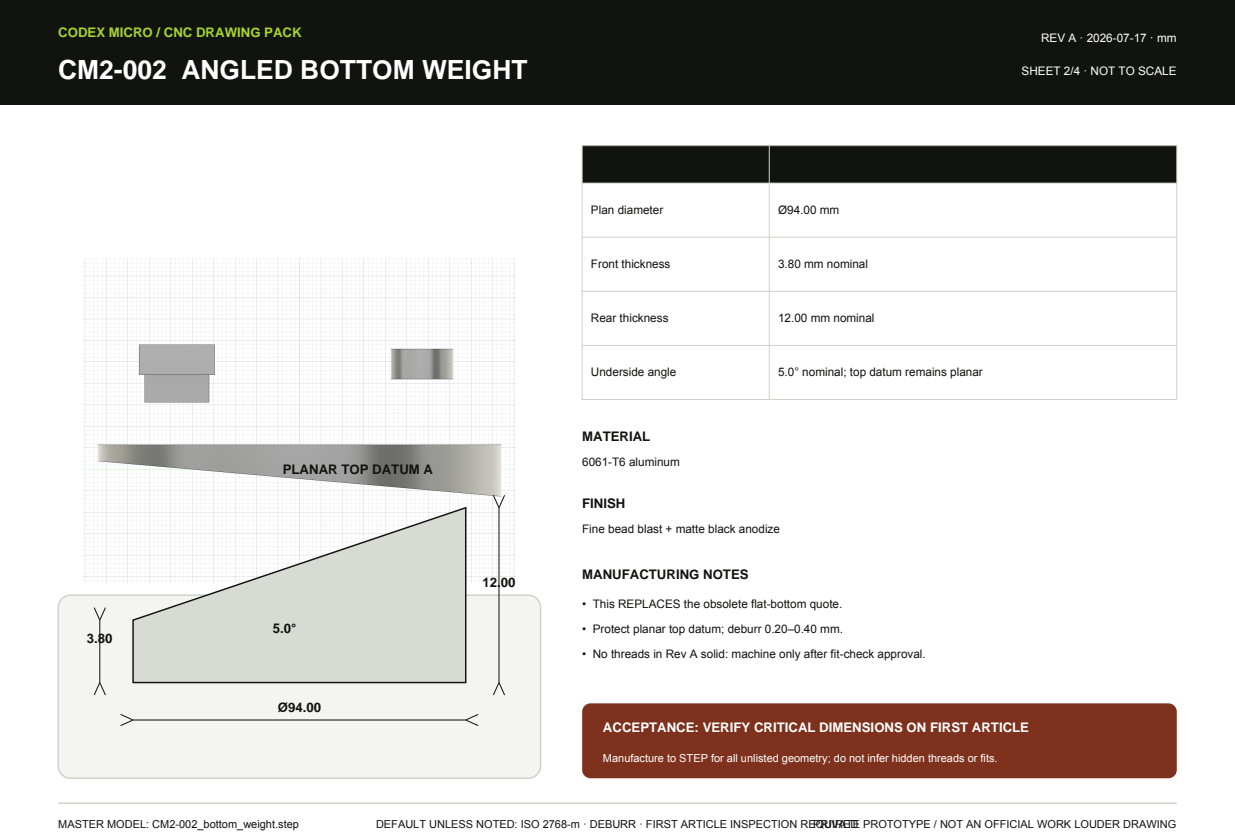
[picture p90: page 2]
MASTER MODEL: CM2-002_bottom_weight.step; DEFAULT UNLESS NOTED: ISO 2768-m · DEBURR · FIRST ARTICLE INSPECTION REQUIRED PRIVATE PROTOTYPE / NOT AN OFFICIAL WORK LOUDER DRAWING; MATERIAL; 6061-T6 aluminum; FINISH; MANUFACTURING NOTES

SHEET 2/4 · NOT TO SCALE

PROPERTY | CONTROLLED REQUIREMENT

Plan diameter | Ø94.00 mm

Front thickness | 3.80 mm nominal

Rear thickness | 12.00 mm nominal

Underside angle | 5.0° nominal; top datum remains planar

PLANAR TOP DATUM A

Fine bead blast + matte black anodize

• This REPLACES the obsolete flat-bottom quote.

• Protect planar top datum; deburr 0.20–0.40 mm.

• No threads in Rev A solid: machine only after fit-check approval.

ACCEPTANCE: VERIFY CRITICAL DIMENSIONS ON FIRST ARTICLE

Manufacture to STEP for all unlisted geometry; do not infer hidden threads or fits.

# CM2-003 OPTIONAL LIGHT PIPE

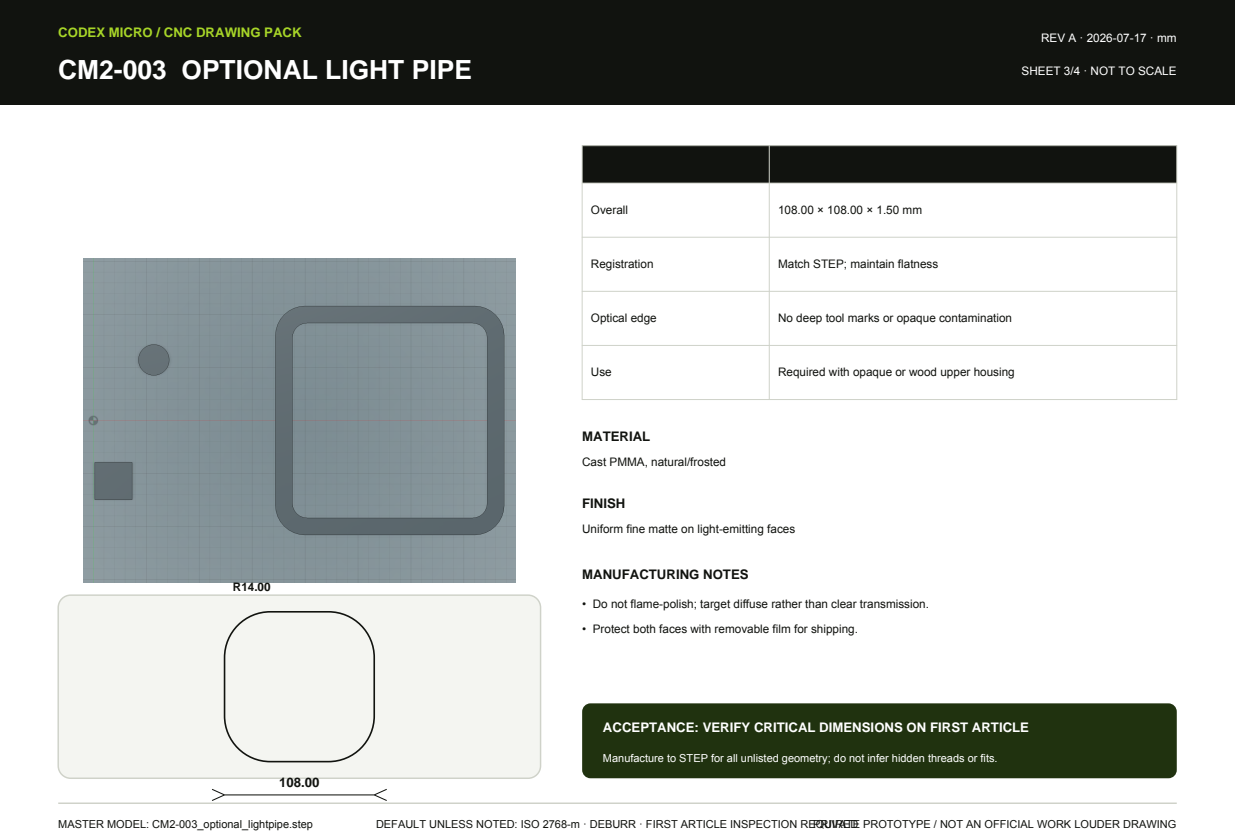
[picture p91: page 3]
MASTER MODEL: CM2-003_optional_lightpipe.step; DEFAULT UNLESS NOTED: ISO 2768-m · DEBURR · FIRST ARTICLE INSPECTION REQUIRED PRIVATE PROTOTYPE / NOT AN OFFICIAL WORK LOUDER DRAWING; MATERIAL; FINISH; MANUFACTURING NOTES

SHEET 3/4 · NOT TO SCALE

PROPERTY | CONTROLLED REQUIREMENT

Overall | 108.00 × 108.00 × 1.50 mm

Registration | Match STEP; maintain flatness

Optical edge | No deep tool marks or opaque contamination

Use | Required with opaque or wood upper housing

Cast PMMA, natural/frosted

Uniform fine matte on light-emitting faces

• Do not flame-polish; target diffuse rather than clear transmission.

• Protect both faces with removable film for shipping.

ACCEPTANCE: VERIFY CRITICAL DIMENSIONS ON FIRST ARTICLE

Manufacture to STEP for all unlisted geometry; do not infer hidden threads or fits.

# CM2-004 JOYSTICK CAP FIT PROTOTYPE

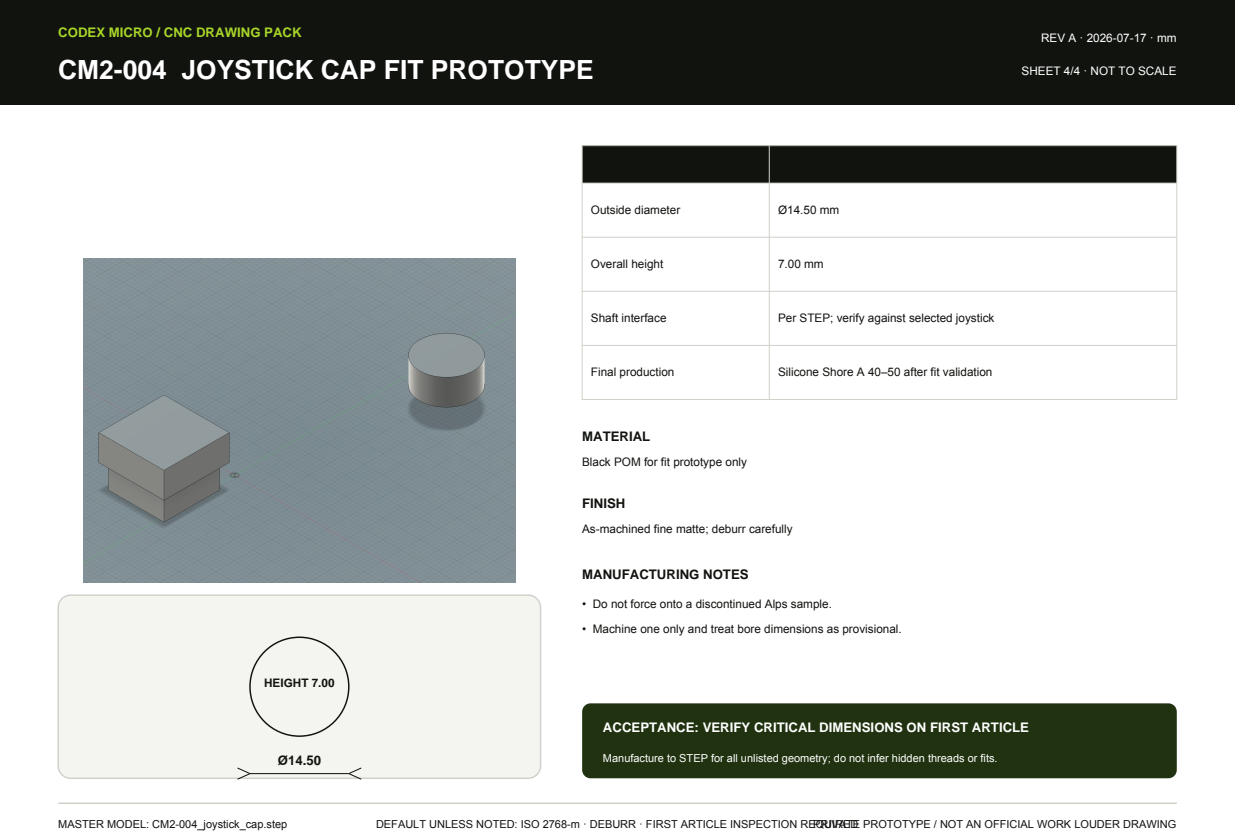
[picture p92: page 4]
MASTER MODEL: CM2-004_joystick_cap.step; DEFAULT UNLESS NOTED: ISO 2768-m · DEBURR · FIRST ARTICLE INSPECTION REQUIRED PRIVATE PROTOTYPE / NOT AN OFFICIAL WORK LOUDER DRAWING; HEIGHT 7.00; MATERIAL; FINISH; MANUFACTURING NOTES

SHEET 4/4 · NOT TO SCALE

PROPERTY | CONTROLLED REQUIREMENT

Outside diameter | Ø14.50 mm

Overall height | 7.00 mm

Shaft interface | Per STEP; verify against selected joystick

Final production | Silicone Shore A 40–50 after fit validation

Black POM for fit prototype only

As-machined fine matte; deburr carefully

• Do not force onto a discontinued Alps sample.

• Machine one only and treat bore dimensions as provisional.

ACCEPTANCE: VERIFY CRITICAL DIMENSIONS ON FIRST ARTICLE

Manufacture to STEP for all unlisted geometry; do not infer hidden threads or fits.
